kcuzner/kl2-dev/firmware/include/MKL26Z4.h

/*
** ###################################################################
**     Processors:          MKL26Z128VFM4
**                          MKL26Z64VFM4
**                          MKL26Z32VM4
**                          MKL26Z128VFT4
**                          MKL26Z64VFT4
**                          MKL26Z32VFT4
**                          MKL26Z256VLH4
**                          MKL26Z128VLH4
**                          MKL26Z64VLH4
**                          MKL26Z32VLH4
**                          MKL26Z256VLK4
**                          MKL26Z256VLL4
**                          MKL26Z128VLL4
**                          MKL26Z256VMC4
**                          MKL26Z128VMC4
**
**     Compilers:           ARM Compiler
**                          Freescale C/C++ for Embedded ARM
**                          GNU C Compiler
**                          IAR ANSI C/C++ Compiler for ARM
**
**     Reference manual:    KL46P121M48SF4RM, Rev.1 Draft A, Aug 2012
**     Version:             rev. 1.0, 2012-12-12
**
**     Abstract:
**         This header file implements peripheral memory map for MKL26Z4
**         processor.
**
**     Copyright: 1997 - 2012 Freescale, Inc. All Rights Reserved.
**
**     http:                 www.freescale.com
**     mail:                 support@freescale.com
**
**     Revisions:
**     - rev. 1.0 (2012-12-12)
**         Initial version.
**
** ###################################################################
*/

/**
 * @file MKL26Z4.h
 * @version 1.0
 * @date 2012-12-12
 * @brief Peripheral memory map for MKL26Z4
 *
 * This header file implements peripheral memory map for MKL26Z4 processor.
 */


/* ----------------------------------------------------------------------------
   -- MCU activation
   ---------------------------------------------------------------------------- */

/* Prevention from multiple including the same memory map */
#if !defined(MCU_MKL26Z4)  /* Check if memory map has not been already included */
#define MCU_MKL26Z4

/* Check if another memory map has not been also included */
#if (defined(MCU_ACTIVE))
  #error MKL26Z4 memory map: There is already included another memory map. Only one memory map can be included.
#endif /* (defined(MCU_ACTIVE)) */
#define MCU_ACTIVE

#include <stdint.h>

/** Memory map major version (memory maps with equal major version number are
 * compatible) */
#define MCU_MEM_MAP_VERSION 0x0100u
/** Memory map minor version */
#define MCU_MEM_MAP_VERSION_MINOR 0x0000u


/* ----------------------------------------------------------------------------
   -- Interrupt vector numbers
   ---------------------------------------------------------------------------- */

/**
 * @addtogroup Interrupt_vector_numbers Interrupt vector numbers
 * @{
 */

/** Interrupt Number Definitions */
typedef enum {
  INT_Initial_Stack_Pointer    = 0,                /**< Initial stack pointer */
  INT_Initial_Program_Counter  = 1,                /**< Initial program counter */
  INT_NMI                      = 2,                /**< Non-maskable interrupt */
  INT_Hard_Fault               = 3,                /**< Hard fault exception */
  INT_Reserved4                = 4,                /**< Reserved interrupt 4 */
  INT_Reserved5                = 5,                /**< Reserved interrupt 5 */
  INT_Reserved6                = 6,                /**< Reserved interrupt 6 */
  INT_Reserved7                = 7,                /**< Reserved interrupt 7 */
  INT_Reserved8                = 8,                /**< Reserved interrupt 8 */
  INT_Reserved9                = 9,                /**< Reserved interrupt 9 */
  INT_Reserved10               = 10,               /**< Reserved interrupt 10 */
  INT_SVCall                   = 11,               /**< A supervisor call exception */
  INT_Reserved12               = 12,               /**< Reserved interrupt 12 */
  INT_Reserved13               = 13,               /**< Reserved interrupt 13 */
  INT_PendableSrvReq           = 14,               /**< PendSV exception - request for system level service */
  INT_SysTick                  = 15,               /**< SysTick interrupt */
  INT_DMA0                     = 16,               /**< DMA channel 0 transfer complete/error interrupt */
  INT_DMA1                     = 17,               /**< DMA channel 1 transfer complete/error interrupt */
  INT_DMA2                     = 18,               /**< DMA channel 2 transfer complete/error interrupt */
  INT_DMA3                     = 19,               /**< DMA channel 3 transfer complete/error interrupt */
  INT_Reserved20               = 20,               /**< Reserved interrupt 20 */
  INT_FTFA                     = 21,               /**< FTFA command complete/read collision interrupt */
  INT_LVD_LVW                  = 22,               /**< Low Voltage Detect, Low Voltage Warning */
  INT_LLW                      = 23,               /**< Low Leakage Wakeup */
  INT_I2C0                     = 24,               /**< I2C0 interrupt */
  INT_I2C1                     = 25,               /**< I2C0 interrupt 25 */
  INT_SPI0                     = 26,               /**< SPI0 interrupt */
  INT_SPI1                     = 27,               /**< SPI1 interrupt */
  INT_UART0                    = 28,               /**< UART0 status/error interrupt */
  INT_UART1                    = 29,               /**< UART1 status/error interrupt */
  INT_UART2                    = 30,               /**< UART2 status/error interrupt */
  INT_ADC0                     = 31,               /**< ADC0 interrupt */
  INT_CMP0                     = 32,               /**< CMP0 interrupt */
  INT_TPM0                     = 33,               /**< TPM0 fault, overflow and channels interrupt */
  INT_TPM1                     = 34,               /**< TPM1 fault, overflow and channels interrupt */
  INT_TPM2                     = 35,               /**< TPM2 fault, overflow and channels interrupt */
  INT_RTC                      = 36,               /**< RTC interrupt */
  INT_RTC_Seconds              = 37,               /**< RTC seconds interrupt */
  INT_PIT                      = 38,               /**< PIT timer interrupt */
  INT_I2S0                     = 39,               /**< I2S0 transmit interrupt */
  INT_USB0                     = 40,               /**< USB0 interrupt */
  INT_DAC0                     = 41,               /**< DAC0 interrupt */
  INT_TSI0                     = 42,               /**< TSI0 interrupt */
  INT_MCG                      = 43,               /**< MCG interrupt */
  INT_LPTimer                  = 44,               /**< LPTimer interrupt */
  INT_Reserved45               = 45,               /**< Reserved interrupt 45 */
  INT_PORTA                    = 46,               /**< Port A interrupt */
  INT_PORTD                    = 47                /**< Port D interrupt */
} IRQInterruptIndex;

/**
 * @}
 */ /* end of group Interrupt_vector_numbers */


/* ----------------------------------------------------------------------------
   -- Peripheral type defines
   ---------------------------------------------------------------------------- */

/**
 * @addtogroup Peripheral_defines Peripheral type defines
 * @{
 */


/*
** Start of section using anonymous unions
*/

#if defined(__ARMCC_VERSION)
  #pragma push
  #pragma anon_unions
#elif defined(__CWCC__)
  #pragma push
  #pragma cpp_extensions on
#elif defined(__GNUC__)
  /* anonymous unions are enabled by default */
#elif defined(__IAR_SYSTEMS_ICC__)
  #pragma language=extended
#else
  #error Not supported compiler type
#endif

/* ----------------------------------------------------------------------------
   -- ADC
   ---------------------------------------------------------------------------- */

/**
 * @addtogroup ADC_Peripheral ADC
 * @{
 */

/** ADC - Peripheral register structure */
typedef struct ADC_MemMap {
  uint32_t SC1[2];                                 /**< ADC Status and Control Registers 1, array offset: 0x0, array step: 0x4 */
  uint32_t CFG1;                                   /**< ADC Configuration Register 1, offset: 0x8 */
  uint32_t CFG2;                                   /**< ADC Configuration Register 2, offset: 0xC */
  uint32_t R[2];                                   /**< ADC Data Result Register, array offset: 0x10, array step: 0x4 */
  uint32_t CV1;                                    /**< Compare Value Registers, offset: 0x18 */
  uint32_t CV2;                                    /**< Compare Value Registers, offset: 0x1C */
  uint32_t SC2;                                    /**< Status and Control Register 2, offset: 0x20 */
  uint32_t SC3;                                    /**< Status and Control Register 3, offset: 0x24 */
  uint32_t OFS;                                    /**< ADC Offset Correction Register, offset: 0x28 */
  uint32_t PG;                                     /**< ADC Plus-Side Gain Register, offset: 0x2C */
  uint32_t MG;                                     /**< ADC Minus-Side Gain Register, offset: 0x30 */
  uint32_t CLPD;                                   /**< ADC Plus-Side General Calibration Value Register, offset: 0x34 */
  uint32_t CLPS;                                   /**< ADC Plus-Side General Calibration Value Register, offset: 0x38 */
  uint32_t CLP4;                                   /**< ADC Plus-Side General Calibration Value Register, offset: 0x3C */
  uint32_t CLP3;                                   /**< ADC Plus-Side General Calibration Value Register, offset: 0x40 */
  uint32_t CLP2;                                   /**< ADC Plus-Side General Calibration Value Register, offset: 0x44 */
  uint32_t CLP1;                                   /**< ADC Plus-Side General Calibration Value Register, offset: 0x48 */
  uint32_t CLP0;                                   /**< ADC Plus-Side General Calibration Value Register, offset: 0x4C */
  uint8_t RESERVED_0[4];
  uint32_t CLMD;                                   /**< ADC Minus-Side General Calibration Value Register, offset: 0x54 */
  uint32_t CLMS;                                   /**< ADC Minus-Side General Calibration Value Register, offset: 0x58 */
  uint32_t CLM4;                                   /**< ADC Minus-Side General Calibration Value Register, offset: 0x5C */
  uint32_t CLM3;                                   /**< ADC Minus-Side General Calibration Value Register, offset: 0x60 */
  uint32_t CLM2;                                   /**< ADC Minus-Side General Calibration Value Register, offset: 0x64 */
  uint32_t CLM1;                                   /**< ADC Minus-Side General Calibration Value Register, offset: 0x68 */
  uint32_t CLM0;                                   /**< ADC Minus-Side General Calibration Value Register, offset: 0x6C */
} volatile *ADC_MemMapPtr;

/* ----------------------------------------------------------------------------
   -- ADC - Register accessor macros
   ---------------------------------------------------------------------------- */

/**
 * @addtogroup ADC_Register_Accessor_Macros ADC - Register accessor macros
 * @{
 */


/* ADC - Register accessors */
#define ADC_SC1_REG(base,index)                  ((base)->SC1[index])
#define ADC_CFG1_REG(base)                       ((base)->CFG1)
#define ADC_CFG2_REG(base)                       ((base)->CFG2)
#define ADC_R_REG(base,index)                    ((base)->R[index])
#define ADC_CV1_REG(base)                        ((base)->CV1)
#define ADC_CV2_REG(base)                        ((base)->CV2)
#define ADC_SC2_REG(base)                        ((base)->SC2)
#define ADC_SC3_REG(base)                        ((base)->SC3)
#define ADC_OFS_REG(base)                        ((base)->OFS)
#define ADC_PG_REG(base)                         ((base)->PG)
#define ADC_MG_REG(base)                         ((base)->MG)
#define ADC_CLPD_REG(base)                       ((base)->CLPD)
#define ADC_CLPS_REG(base)                       ((base)->CLPS)
#define ADC_CLP4_REG(base)                       ((base)->CLP4)
#define ADC_CLP3_REG(base)                       ((base)->CLP3)
#define ADC_CLP2_REG(base)                       ((base)->CLP2)
#define ADC_CLP1_REG(base)                       ((base)->CLP1)
#define ADC_CLP0_REG(base)                       ((base)->CLP0)
#define ADC_CLMD_REG(base)                       ((base)->CLMD)
#define ADC_CLMS_REG(base)                       ((base)->CLMS)
#define ADC_CLM4_REG(base)                       ((base)->CLM4)
#define ADC_CLM3_REG(base)                       ((base)->CLM3)
#define ADC_CLM2_REG(base)                       ((base)->CLM2)
#define ADC_CLM1_REG(base)                       ((base)->CLM1)
#define ADC_CLM0_REG(base)                       ((base)->CLM0)

/**
 * @}
 */ /* end of group ADC_Register_Accessor_Macros */


/* ----------------------------------------------------------------------------
   -- ADC Register Masks
   ---------------------------------------------------------------------------- */

/**
 * @addtogroup ADC_Register_Masks ADC Register Masks
 * @{
 */

/* SC1 Bit Fields */
#define ADC_SC1_ADCH_MASK                        0x1Fu
#define ADC_SC1_ADCH_SHIFT                       0
#define ADC_SC1_ADCH(x)                          (((uint32_t)(((uint32_t)(x))<<ADC_SC1_ADCH_SHIFT))&ADC_SC1_ADCH_MASK)
#define ADC_SC1_DIFF_MASK                        0x20u
#define ADC_SC1_DIFF_SHIFT                       5
#define ADC_SC1_AIEN_MASK                        0x40u
#define ADC_SC1_AIEN_SHIFT                       6
#define ADC_SC1_COCO_MASK                        0x80u
#define ADC_SC1_COCO_SHIFT                       7
/* CFG1 Bit Fields */
#define ADC_CFG1_ADICLK_MASK                     0x3u
#define ADC_CFG1_ADICLK_SHIFT                    0
#define ADC_CFG1_ADICLK(x)                       (((uint32_t)(((uint32_t)(x))<<ADC_CFG1_ADICLK_SHIFT))&ADC_CFG1_ADICLK_MASK)
#define ADC_CFG1_MODE_MASK                       0xCu
#define ADC_CFG1_MODE_SHIFT                      2
#define ADC_CFG1_MODE(x)                         (((uint32_t)(((uint32_t)(x))<<ADC_CFG1_MODE_SHIFT))&ADC_CFG1_MODE_MASK)
#define ADC_CFG1_ADLSMP_MASK                     0x10u
#define ADC_CFG1_ADLSMP_SHIFT                    4
#define ADC_CFG1_ADIV_MASK                       0x60u
#define ADC_CFG1_ADIV_SHIFT                      5
#define ADC_CFG1_ADIV(x)                         (((uint32_t)(((uint32_t)(x))<<ADC_CFG1_ADIV_SHIFT))&ADC_CFG1_ADIV_MASK)
#define ADC_CFG1_ADLPC_MASK                      0x80u
#define ADC_CFG1_ADLPC_SHIFT                     7
/* CFG2 Bit Fields */
#define ADC_CFG2_ADLSTS_MASK                     0x3u
#define ADC_CFG2_ADLSTS_SHIFT                    0
#define ADC_CFG2_ADLSTS(x)                       (((uint32_t)(((uint32_t)(x))<<ADC_CFG2_ADLSTS_SHIFT))&ADC_CFG2_ADLSTS_MASK)
#define ADC_CFG2_ADHSC_MASK                      0x4u
#define ADC_CFG2_ADHSC_SHIFT                     2
#define ADC_CFG2_ADACKEN_MASK                    0x8u
#define ADC_CFG2_ADACKEN_SHIFT                   3
#define ADC_CFG2_MUXSEL_MASK                     0x10u
#define ADC_CFG2_MUXSEL_SHIFT                    4
/* R Bit Fields */
#define ADC_R_D_MASK                             0xFFFFu
#define ADC_R_D_SHIFT                            0
#define ADC_R_D(x)                               (((uint32_t)(((uint32_t)(x))<<ADC_R_D_SHIFT))&ADC_R_D_MASK)
/* CV1 Bit Fields */
#define ADC_CV1_CV_MASK                          0xFFFFu
#define ADC_CV1_CV_SHIFT                         0
#define ADC_CV1_CV(x)                            (((uint32_t)(((uint32_t)(x))<<ADC_CV1_CV_SHIFT))&ADC_CV1_CV_MASK)
/* CV2 Bit Fields */
#define ADC_CV2_CV_MASK                          0xFFFFu
#define ADC_CV2_CV_SHIFT                         0
#define ADC_CV2_CV(x)                            (((uint32_t)(((uint32_t)(x))<<ADC_CV2_CV_SHIFT))&ADC_CV2_CV_MASK)
/* SC2 Bit Fields */
#define ADC_SC2_REFSEL_MASK                      0x3u
#define ADC_SC2_REFSEL_SHIFT                     0
#define ADC_SC2_REFSEL(x)                        (((uint32_t)(((uint32_t)(x))<<ADC_SC2_REFSEL_SHIFT))&ADC_SC2_REFSEL_MASK)
#define ADC_SC2_DMAEN_MASK                       0x4u
#define ADC_SC2_DMAEN_SHIFT                      2
#define ADC_SC2_ACREN_MASK                       0x8u
#define ADC_SC2_ACREN_SHIFT                      3
#define ADC_SC2_ACFGT_MASK                       0x10u
#define ADC_SC2_ACFGT_SHIFT                      4
#define ADC_SC2_ACFE_MASK                        0x20u
#define ADC_SC2_ACFE_SHIFT                       5
#define ADC_SC2_ADTRG_MASK                       0x40u
#define ADC_SC2_ADTRG_SHIFT                      6
#define ADC_SC2_ADACT_MASK                       0x80u
#define ADC_SC2_ADACT_SHIFT                      7
/* SC3 Bit Fields */
#define ADC_SC3_AVGS_MASK                        0x3u
#define ADC_SC3_AVGS_SHIFT                       0
#define ADC_SC3_AVGS(x)                          (((uint32_t)(((uint32_t)(x))<<ADC_SC3_AVGS_SHIFT))&ADC_SC3_AVGS_MASK)
#define ADC_SC3_AVGE_MASK                        0x4u
#define ADC_SC3_AVGE_SHIFT                       2
#define ADC_SC3_ADCO_MASK                        0x8u
#define ADC_SC3_ADCO_SHIFT                       3
#define ADC_SC3_CALF_MASK                        0x40u
#define ADC_SC3_CALF_SHIFT                       6
#define ADC_SC3_CAL_MASK                         0x80u
#define ADC_SC3_CAL_SHIFT                        7
/* OFS Bit Fields */
#define ADC_OFS_OFS_MASK                         0xFFFFu
#define ADC_OFS_OFS_SHIFT                        0
#define ADC_OFS_OFS(x)                           (((uint32_t)(((uint32_t)(x))<<ADC_OFS_OFS_SHIFT))&ADC_OFS_OFS_MASK)
/* PG Bit Fields */
#define ADC_PG_PG_MASK                           0xFFFFu
#define ADC_PG_PG_SHIFT                          0
#define ADC_PG_PG(x)                             (((uint32_t)(((uint32_t)(x))<<ADC_PG_PG_SHIFT))&ADC_PG_PG_MASK)
/* MG Bit Fields */
#define ADC_MG_MG_MASK                           0xFFFFu
#define ADC_MG_MG_SHIFT                          0
#define ADC_MG_MG(x)                             (((uint32_t)(((uint32_t)(x))<<ADC_MG_MG_SHIFT))&ADC_MG_MG_MASK)
/* CLPD Bit Fields */
#define ADC_CLPD_CLPD_MASK                       0x3Fu
#define ADC_CLPD_CLPD_SHIFT                      0
#define ADC_CLPD_CLPD(x)                         (((uint32_t)(((uint32_t)(x))<<ADC_CLPD_CLPD_SHIFT))&ADC_CLPD_CLPD_MASK)
/* CLPS Bit Fields */
#define ADC_CLPS_CLPS_MASK                       0x3Fu
#define ADC_CLPS_CLPS_SHIFT                      0
#define ADC_CLPS_CLPS(x)                         (((uint32_t)(((uint32_t)(x))<<ADC_CLPS_CLPS_SHIFT))&ADC_CLPS_CLPS_MASK)
/* CLP4 Bit Fields */
#define ADC_CLP4_CLP4_MASK                       0x3FFu
#define ADC_CLP4_CLP4_SHIFT                      0
#define ADC_CLP4_CLP4(x)                         (((uint32_t)(((uint32_t)(x))<<ADC_CLP4_CLP4_SHIFT))&ADC_CLP4_CLP4_MASK)
/* CLP3 Bit Fields */
#define ADC_CLP3_CLP3_MASK                       0x1FFu
#define ADC_CLP3_CLP3_SHIFT                      0
#define ADC_CLP3_CLP3(x)                         (((uint32_t)(((uint32_t)(x))<<ADC_CLP3_CLP3_SHIFT))&ADC_CLP3_CLP3_MASK)
/* CLP2 Bit Fields */
#define ADC_CLP2_CLP2_MASK                       0xFFu
#define ADC_CLP2_CLP2_SHIFT                      0
#define ADC_CLP2_CLP2(x)                         (((uint32_t)(((uint32_t)(x))<<ADC_CLP2_CLP2_SHIFT))&ADC_CLP2_CLP2_MASK)
/* CLP1 Bit Fields */
#define ADC_CLP1_CLP1_MASK                       0x7Fu
#define ADC_CLP1_CLP1_SHIFT                      0
#define ADC_CLP1_CLP1(x)                         (((uint32_t)(((uint32_t)(x))<<ADC_CLP1_CLP1_SHIFT))&ADC_CLP1_CLP1_MASK)
/* CLP0 Bit Fields */
#define ADC_CLP0_CLP0_MASK                       0x3Fu
#define ADC_CLP0_CLP0_SHIFT                      0
#define ADC_CLP0_CLP0(x)                         (((uint32_t)(((uint32_t)(x))<<ADC_CLP0_CLP0_SHIFT))&ADC_CLP0_CLP0_MASK)
/* CLMD Bit Fields */
#define ADC_CLMD_CLMD_MASK                       0x3Fu
#define ADC_CLMD_CLMD_SHIFT                      0
#define ADC_CLMD_CLMD(x)                         (((uint32_t)(((uint32_t)(x))<<ADC_CLMD_CLMD_SHIFT))&ADC_CLMD_CLMD_MASK)
/* CLMS Bit Fields */
#define ADC_CLMS_CLMS_MASK                       0x3Fu
#define ADC_CLMS_CLMS_SHIFT                      0
#define ADC_CLMS_CLMS(x)                         (((uint32_t)(((uint32_t)(x))<<ADC_CLMS_CLMS_SHIFT))&ADC_CLMS_CLMS_MASK)
/* CLM4 Bit Fields */
#define ADC_CLM4_CLM4_MASK                       0x3FFu
#define ADC_CLM4_CLM4_SHIFT                      0
#define ADC_CLM4_CLM4(x)                         (((uint32_t)(((uint32_t)(x))<<ADC_CLM4_CLM4_SHIFT))&ADC_CLM4_CLM4_MASK)
/* CLM3 Bit Fields */
#define ADC_CLM3_CLM3_MASK                       0x1FFu
#define ADC_CLM3_CLM3_SHIFT                      0
#define ADC_CLM3_CLM3(x)                         (((uint32_t)(((uint32_t)(x))<<ADC_CLM3_CLM3_SHIFT))&ADC_CLM3_CLM3_MASK)
/* CLM2 Bit Fields */
#define ADC_CLM2_CLM2_MASK                       0xFFu
#define ADC_CLM2_CLM2_SHIFT                      0
#define ADC_CLM2_CLM2(x)                         (((uint32_t)(((uint32_t)(x))<<ADC_CLM2_CLM2_SHIFT))&ADC_CLM2_CLM2_MASK)
/* CLM1 Bit Fields */
#define ADC_CLM1_CLM1_MASK                       0x7Fu
#define ADC_CLM1_CLM1_SHIFT                      0
#define ADC_CLM1_CLM1(x)                         (((uint32_t)(((uint32_t)(x))<<ADC_CLM1_CLM1_SHIFT))&ADC_CLM1_CLM1_MASK)
/* CLM0 Bit Fields */
#define ADC_CLM0_CLM0_MASK                       0x3Fu
#define ADC_CLM0_CLM0_SHIFT                      0
#define ADC_CLM0_CLM0(x)                         (((uint32_t)(((uint32_t)(x))<<ADC_CLM0_CLM0_SHIFT))&ADC_CLM0_CLM0_MASK)

/**
 * @}
 */ /* end of group ADC_Register_Masks */


/* ADC - Peripheral instance base addresses */
/** Peripheral ADC0 base pointer */
#define ADC0_BASE_PTR                            ((ADC_MemMapPtr)0x4003B000u)
/** Array initializer of ADC peripheral base pointers */
#define ADC_BASE_PTRS                            { ADC0_BASE_PTR }

/* ----------------------------------------------------------------------------
   -- ADC - Register accessor macros
   ---------------------------------------------------------------------------- */

/**
 * @addtogroup ADC_Register_Accessor_Macros ADC - Register accessor macros
 * @{
 */


/* ADC - Register instance definitions */
/* ADC0 */
#define ADC0_SC1A                                ADC_SC1_REG(ADC0_BASE_PTR,0)
#define ADC0_SC1B                                ADC_SC1_REG(ADC0_BASE_PTR,1)
#define ADC0_CFG1                                ADC_CFG1_REG(ADC0_BASE_PTR)
#define ADC0_CFG2                                ADC_CFG2_REG(ADC0_BASE_PTR)
#define ADC0_RA                                  ADC_R_REG(ADC0_BASE_PTR,0)
#define ADC0_RB                                  ADC_R_REG(ADC0_BASE_PTR,1)
#define ADC0_CV1                                 ADC_CV1_REG(ADC0_BASE_PTR)
#define ADC0_CV2                                 ADC_CV2_REG(ADC0_BASE_PTR)
#define ADC0_SC2                                 ADC_SC2_REG(ADC0_BASE_PTR)
#define ADC0_SC3                                 ADC_SC3_REG(ADC0_BASE_PTR)
#define ADC0_OFS                                 ADC_OFS_REG(ADC0_BASE_PTR)
#define ADC0_PG                                  ADC_PG_REG(ADC0_BASE_PTR)
#define ADC0_MG                                  ADC_MG_REG(ADC0_BASE_PTR)
#define ADC0_CLPD                                ADC_CLPD_REG(ADC0_BASE_PTR)
#define ADC0_CLPS                                ADC_CLPS_REG(ADC0_BASE_PTR)
#define ADC0_CLP4                                ADC_CLP4_REG(ADC0_BASE_PTR)
#define ADC0_CLP3                                ADC_CLP3_REG(ADC0_BASE_PTR)
#define ADC0_CLP2                                ADC_CLP2_REG(ADC0_BASE_PTR)
#define ADC0_CLP1                                ADC_CLP1_REG(ADC0_BASE_PTR)
#define ADC0_CLP0                                ADC_CLP0_REG(ADC0_BASE_PTR)
#define ADC0_CLMD                                ADC_CLMD_REG(ADC0_BASE_PTR)
#define ADC0_CLMS                                ADC_CLMS_REG(ADC0_BASE_PTR)
#define ADC0_CLM4                                ADC_CLM4_REG(ADC0_BASE_PTR)
#define ADC0_CLM3                                ADC_CLM3_REG(ADC0_BASE_PTR)
#define ADC0_CLM2                                ADC_CLM2_REG(ADC0_BASE_PTR)
#define ADC0_CLM1                                ADC_CLM1_REG(ADC0_BASE_PTR)
#define ADC0_CLM0                                ADC_CLM0_REG(ADC0_BASE_PTR)

/* ADC - Register array accessors */
#define ADC0_SC1(index)                          ADC_SC1_REG(ADC0_BASE_PTR,index)
#define ADC0_R(index)                            ADC_R_REG(ADC0_BASE_PTR,index)

/**
 * @}
 */ /* end of group ADC_Register_Accessor_Macros */


/**
 * @}
 */ /* end of group ADC_Peripheral */


/* ----------------------------------------------------------------------------
   -- BP
   ---------------------------------------------------------------------------- */

/**
 * @addtogroup BP_Peripheral BP
 * @{
 */

/** BP - Peripheral register structure */
typedef struct BP_MemMap {
  uint32_t CTRL;                                   /**< FlashPatch Control Register, offset: 0x0 */
  uint8_t RESERVED_0[4];
  uint32_t COMP[2];                                /**< FlashPatch Comparator Register 0..FlashPatch Comparator Register 1, array offset: 0x8, array step: 0x4 */
  uint8_t RESERVED_1[4032];
  uint32_t PID4;                                   /**< Peripheral Identification Register 4., offset: 0xFD0 */
  uint32_t PID5;                                   /**< Peripheral Identification Register 5., offset: 0xFD4 */
  uint32_t PID6;                                   /**< Peripheral Identification Register 6., offset: 0xFD8 */
  uint32_t PID7;                                   /**< Peripheral Identification Register 7., offset: 0xFDC */
  uint32_t PID0;                                   /**< Peripheral Identification Register 0., offset: 0xFE0 */
  uint32_t PID1;                                   /**< Peripheral Identification Register 1., offset: 0xFE4 */
  uint32_t PID2;                                   /**< Peripheral Identification Register 2., offset: 0xFE8 */
  uint32_t PID3;                                   /**< Peripheral Identification Register 3., offset: 0xFEC */
  uint32_t CID0;                                   /**< Component Identification Register 0., offset: 0xFF0 */
  uint32_t CID1;                                   /**< Component Identification Register 1., offset: 0xFF4 */
  uint32_t CID2;                                   /**< Component Identification Register 2., offset: 0xFF8 */
  uint32_t CID3;                                   /**< Component Identification Register 3., offset: 0xFFC */
} volatile *BP_MemMapPtr;

/* ----------------------------------------------------------------------------
   -- BP - Register accessor macros
   ---------------------------------------------------------------------------- */

/**
 * @addtogroup BP_Register_Accessor_Macros BP - Register accessor macros
 * @{
 */


/* BP - Register accessors */
#define BP_CTRL_REG(base)                        ((base)->CTRL)
#define BP_COMP_REG(base,index)                  ((base)->COMP[index])
#define BP_PID4_REG(base)                        ((base)->PID4)
#define BP_PID5_REG(base)                        ((base)->PID5)
#define BP_PID6_REG(base)                        ((base)->PID6)
#define BP_PID7_REG(base)                        ((base)->PID7)
#define BP_PID0_REG(base)                        ((base)->PID0)
#define BP_PID1_REG(base)                        ((base)->PID1)
#define BP_PID2_REG(base)                        ((base)->PID2)
#define BP_PID3_REG(base)                        ((base)->PID3)
#define BP_CID0_REG(base)                        ((base)->CID0)
#define BP_CID1_REG(base)                        ((base)->CID1)
#define BP_CID2_REG(base)                        ((base)->CID2)
#define BP_CID3_REG(base)                        ((base)->CID3)

/**
 * @}
 */ /* end of group BP_Register_Accessor_Macros */


/* ----------------------------------------------------------------------------
   -- BP Register Masks
   ---------------------------------------------------------------------------- */

/**
 * @addtogroup BP_Register_Masks BP Register Masks
 * @{
 */


/**
 * @}
 */ /* end of group BP_Register_Masks */


/* BP - Peripheral instance base addresses */
/** Peripheral BP base pointer */
#define BP_BASE_PTR                              ((BP_MemMapPtr)0xE0002000u)
/** Array initializer of BP peripheral base pointers */
#define BP_BASE_PTRS                             { BP_BASE_PTR }

/* ----------------------------------------------------------------------------
   -- BP - Register accessor macros
   ---------------------------------------------------------------------------- */

/**
 * @addtogroup BP_Register_Accessor_Macros BP - Register accessor macros
 * @{
 */


/* BP - Register instance definitions */
/* BP */
#define BP_CTRL                                  BP_CTRL_REG(BP_BASE_PTR)
#define BP_COMP0                                 BP_COMP_REG(BP_BASE_PTR,0)
#define BP_COMP1                                 BP_COMP_REG(BP_BASE_PTR,1)
#define BP_PID4                                  BP_PID4_REG(BP_BASE_PTR)
#define BP_PID5                                  BP_PID5_REG(BP_BASE_PTR)
#define BP_PID6                                  BP_PID6_REG(BP_BASE_PTR)
#define BP_PID7                                  BP_PID7_REG(BP_BASE_PTR)
#define BP_PID0                                  BP_PID0_REG(BP_BASE_PTR)
#define BP_PID1                                  BP_PID1_REG(BP_BASE_PTR)
#define BP_PID2                                  BP_PID2_REG(BP_BASE_PTR)
#define BP_PID3                                  BP_PID3_REG(BP_BASE_PTR)
#define BP_CID0                                  BP_CID0_REG(BP_BASE_PTR)
#define BP_CID1                                  BP_CID1_REG(BP_BASE_PTR)
#define BP_CID2                                  BP_CID2_REG(BP_BASE_PTR)
#define BP_CID3                                  BP_CID3_REG(BP_BASE_PTR)

/* BP - Register array accessors */
#define BP_COMP(index)                           BP_COMP_REG(BP_BASE_PTR,index)

/**
 * @}
 */ /* end of group BP_Register_Accessor_Macros */


/**
 * @}
 */ /* end of group BP_Peripheral */


/* ----------------------------------------------------------------------------
   -- CMP
   ---------------------------------------------------------------------------- */

/**
 * @addtogroup CMP_Peripheral CMP
 * @{
 */

/** CMP - Peripheral register structure */
typedef struct CMP_MemMap {
  uint8_t CR0;                                     /**< CMP Control Register 0, offset: 0x0 */
  uint8_t CR1;                                     /**< CMP Control Register 1, offset: 0x1 */
  uint8_t FPR;                                     /**< CMP Filter Period Register, offset: 0x2 */
  uint8_t SCR;                                     /**< CMP Status and Control Register, offset: 0x3 */
  uint8_t DACCR;                                   /**< DAC Control Register, offset: 0x4 */
  uint8_t MUXCR;                                   /**< MUX Control Register, offset: 0x5 */
} volatile *CMP_MemMapPtr;

/* ----------------------------------------------------------------------------
   -- CMP - Register accessor macros
   ---------------------------------------------------------------------------- */

/**
 * @addtogroup CMP_Register_Accessor_Macros CMP - Register accessor macros
 * @{
 */


/* CMP - Register accessors */
#define CMP_CR0_REG(base)                        ((base)->CR0)
#define CMP_CR1_REG(base)                        ((base)->CR1)
#define CMP_FPR_REG(base)                        ((base)->FPR)
#define CMP_SCR_REG(base)                        ((base)->SCR)
#define CMP_DACCR_REG(base)                      ((base)->DACCR)
#define CMP_MUXCR_REG(base)                      ((base)->MUXCR)

/**
 * @}
 */ /* end of group CMP_Register_Accessor_Macros */


/* ----------------------------------------------------------------------------
   -- CMP Register Masks
   ---------------------------------------------------------------------------- */

/**
 * @addtogroup CMP_Register_Masks CMP Register Masks
 * @{
 */

/* CR0 Bit Fields */
#define CMP_CR0_HYSTCTR_MASK                     0x3u
#define CMP_CR0_HYSTCTR_SHIFT                    0
#define CMP_CR0_HYSTCTR(x)                       (((uint8_t)(((uint8_t)(x))<<CMP_CR0_HYSTCTR_SHIFT))&CMP_CR0_HYSTCTR_MASK)
#define CMP_CR0_FILTER_CNT_MASK                  0x70u
#define CMP_CR0_FILTER_CNT_SHIFT                 4
#define CMP_CR0_FILTER_CNT(x)                    (((uint8_t)(((uint8_t)(x))<<CMP_CR0_FILTER_CNT_SHIFT))&CMP_CR0_FILTER_CNT_MASK)
/* CR1 Bit Fields */
#define CMP_CR1_EN_MASK                          0x1u
#define CMP_CR1_EN_SHIFT                         0
#define CMP_CR1_OPE_MASK                         0x2u
#define CMP_CR1_OPE_SHIFT                        1
#define CMP_CR1_COS_MASK                         0x4u
#define CMP_CR1_COS_SHIFT                        2
#define CMP_CR1_INV_MASK                         0x8u
#define CMP_CR1_INV_SHIFT                        3
#define CMP_CR1_PMODE_MASK                       0x10u
#define CMP_CR1_PMODE_SHIFT                      4
#define CMP_CR1_TRIGM_MASK                       0x20u
#define CMP_CR1_TRIGM_SHIFT                      5
#define CMP_CR1_WE_MASK                          0x40u
#define CMP_CR1_WE_SHIFT                         6
#define CMP_CR1_SE_MASK                          0x80u
#define CMP_CR1_SE_SHIFT                         7
/* FPR Bit Fields */
#define CMP_FPR_FILT_PER_MASK                    0xFFu
#define CMP_FPR_FILT_PER_SHIFT                   0
#define CMP_FPR_FILT_PER(x)                      (((uint8_t)(((uint8_t)(x))<<CMP_FPR_FILT_PER_SHIFT))&CMP_FPR_FILT_PER_MASK)
/* SCR Bit Fields */
#define CMP_SCR_COUT_MASK                        0x1u
#define CMP_SCR_COUT_SHIFT                       0
#define CMP_SCR_CFF_MASK                         0x2u
#define CMP_SCR_CFF_SHIFT                        1
#define CMP_SCR_CFR_MASK                         0x4u
#define CMP_SCR_CFR_SHIFT                        2
#define CMP_SCR_IEF_MASK                         0x8u
#define CMP_SCR_IEF_SHIFT                        3
#define CMP_SCR_IER_MASK                         0x10u
#define CMP_SCR_IER_SHIFT                        4
#define CMP_SCR_DMAEN_MASK                       0x40u
#define CMP_SCR_DMAEN_SHIFT                      6
/* DACCR Bit Fields */
#define CMP_DACCR_VOSEL_MASK                     0x3Fu
#define CMP_DACCR_VOSEL_SHIFT                    0
#define CMP_DACCR_VOSEL(x)                       (((uint8_t)(((uint8_t)(x))<<CMP_DACCR_VOSEL_SHIFT))&CMP_DACCR_VOSEL_MASK)
#define CMP_DACCR_VRSEL_MASK                     0x40u
#define CMP_DACCR_VRSEL_SHIFT                    6
#define CMP_DACCR_DACEN_MASK                     0x80u
#define CMP_DACCR_DACEN_SHIFT                    7
/* MUXCR Bit Fields */
#define CMP_MUXCR_MSEL_MASK                      0x7u
#define CMP_MUXCR_MSEL_SHIFT                     0
#define CMP_MUXCR_MSEL(x)                        (((uint8_t)(((uint8_t)(x))<<CMP_MUXCR_MSEL_SHIFT))&CMP_MUXCR_MSEL_MASK)
#define CMP_MUXCR_PSEL_MASK                      0x38u
#define CMP_MUXCR_PSEL_SHIFT                     3
#define CMP_MUXCR_PSEL(x)                        (((uint8_t)(((uint8_t)(x))<<CMP_MUXCR_PSEL_SHIFT))&CMP_MUXCR_PSEL_MASK)
#define CMP_MUXCR_PSTM_MASK                      0x80u
#define CMP_MUXCR_PSTM_SHIFT                     7

/**
 * @}
 */ /* end of group CMP_Register_Masks */


/* CMP - Peripheral instance base addresses */
/** Peripheral CMP0 base pointer */
#define CMP0_BASE_PTR                            ((CMP_MemMapPtr)0x40073000u)
/** Array initializer of CMP peripheral base pointers */
#define CMP_BASE_PTRS                            { CMP0_BASE_PTR }

/* ----------------------------------------------------------------------------
   -- CMP - Register accessor macros
   ---------------------------------------------------------------------------- */

/**
 * @addtogroup CMP_Register_Accessor_Macros CMP - Register accessor macros
 * @{
 */


/* CMP - Register instance definitions */
/* CMP0 */
#define CMP0_CR0                                 CMP_CR0_REG(CMP0_BASE_PTR)
#define CMP0_CR1                                 CMP_CR1_REG(CMP0_BASE_PTR)
#define CMP0_FPR                                 CMP_FPR_REG(CMP0_BASE_PTR)
#define CMP0_SCR                                 CMP_SCR_REG(CMP0_BASE_PTR)
#define CMP0_DACCR                               CMP_DACCR_REG(CMP0_BASE_PTR)
#define CMP0_MUXCR                               CMP_MUXCR_REG(CMP0_BASE_PTR)

/**
 * @}
 */ /* end of group CMP_Register_Accessor_Macros */


/**
 * @}
 */ /* end of group CMP_Peripheral */


/* ----------------------------------------------------------------------------
   -- CoreDebug
   ---------------------------------------------------------------------------- */

/**
 * @addtogroup CoreDebug_Peripheral CoreDebug
 * @{
 */

/** CoreDebug - Peripheral register structure */
typedef struct CoreDebug_MemMap {
  union {                                          /* offset: 0x0 */
    uint32_t base_DHCSR_Read;                        /**< Debug Halting Control and Status Register, offset: 0x0 */
    uint32_t base_DHCSR_Write;                       /**< Debug Halting Control and Status Register, offset: 0x0 */
  };
  uint32_t base_DCRSR;                             /**< Debug Core Register Selector Register, offset: 0x4 */
  uint32_t base_DCRDR;                             /**< Debug Core Register Data Register, offset: 0x8 */
  uint32_t base_DEMCR;                             /**< Debug Exception and Monitor Control Register, offset: 0xC */
} volatile *CoreDebug_MemMapPtr;

/* ----------------------------------------------------------------------------
   -- CoreDebug - Register accessor macros
   ---------------------------------------------------------------------------- */

/**
 * @addtogroup CoreDebug_Register_Accessor_Macros CoreDebug - Register accessor macros
 * @{
 */


/* CoreDebug - Register accessors */
#define CoreDebug_base_DHCSR_Read_REG(base)      ((base)->base_DHCSR_Read)
#define CoreDebug_base_DHCSR_Write_REG(base)     ((base)->base_DHCSR_Write)
#define CoreDebug_base_DCRSR_REG(base)           ((base)->base_DCRSR)
#define CoreDebug_base_DCRDR_REG(base)           ((base)->base_DCRDR)
#define CoreDebug_base_DEMCR_REG(base)           ((base)->base_DEMCR)

/**
 * @}
 */ /* end of group CoreDebug_Register_Accessor_Macros */


/* ----------------------------------------------------------------------------
   -- CoreDebug Register Masks
   ---------------------------------------------------------------------------- */

/**
 * @addtogroup CoreDebug_Register_Masks CoreDebug Register Masks
 * @{
 */


/**
 * @}
 */ /* end of group CoreDebug_Register_Masks */


/* CoreDebug - Peripheral instance base addresses */
/** Peripheral CoreDebug base pointer */
#define CoreDebug_BASE_PTR                       ((CoreDebug_MemMapPtr)0xE000EDF0u)
/** Array initializer of CoreDebug peripheral base pointers */
#define CoreDebug_BASE_PTRS                      { CoreDebug_BASE_PTR }

/* ----------------------------------------------------------------------------
   -- CoreDebug - Register accessor macros
   ---------------------------------------------------------------------------- */

/**
 * @addtogroup CoreDebug_Register_Accessor_Macros CoreDebug - Register accessor macros
 * @{
 */


/* CoreDebug - Register instance definitions */
/* CoreDebug */
#define DHCSR_Read                               CoreDebug_base_DHCSR_Read_REG(CoreDebug_BASE_PTR)
#define DHCSR_Write                              CoreDebug_base_DHCSR_Write_REG(CoreDebug_BASE_PTR)
#define DCRSR                                    CoreDebug_base_DCRSR_REG(CoreDebug_BASE_PTR)
#define DCRDR                                    CoreDebug_base_DCRDR_REG(CoreDebug_BASE_PTR)
#define DEMCR                                    CoreDebug_base_DEMCR_REG(CoreDebug_BASE_PTR)

/**
 * @}
 */ /* end of group CoreDebug_Register_Accessor_Macros */


/**
 * @}
 */ /* end of group CoreDebug_Peripheral */


/* ----------------------------------------------------------------------------
   -- DAC
   ---------------------------------------------------------------------------- */

/**
 * @addtogroup DAC_Peripheral DAC
 * @{
 */

/** DAC - Peripheral register structure */
typedef struct DAC_MemMap {
  struct {                                         /* offset: 0x0, array step: 0x2 */
    uint8_t DATL;                                    /**< DAC Data Low Register, array offset: 0x0, array step: 0x2 */
    uint8_t DATH;                                    /**< DAC Data High Register, array offset: 0x1, array step: 0x2 */
  } DAT[2];
  uint8_t RESERVED_0[28];
  uint8_t SR;                                      /**< DAC Status Register, offset: 0x20 */
  uint8_t C0;                                      /**< DAC Control Register, offset: 0x21 */
  uint8_t C1;                                      /**< DAC Control Register 1, offset: 0x22 */
  uint8_t C2;                                      /**< DAC Control Register 2, offset: 0x23 */
} volatile *DAC_MemMapPtr;

/* ----------------------------------------------------------------------------
   -- DAC - Register accessor macros
   ---------------------------------------------------------------------------- */

/**
 * @addtogroup DAC_Register_Accessor_Macros DAC - Register accessor macros
 * @{
 */


/* DAC - Register accessors */
#define DAC_DATL_REG(base,index)                 ((base)->DAT[index].DATL)
#define DAC_DATH_REG(base,index)                 ((base)->DAT[index].DATH)
#define DAC_SR_REG(base)                         ((base)->SR)
#define DAC_C0_REG(base)                         ((base)->C0)
#define DAC_C1_REG(base)                         ((base)->C1)
#define DAC_C2_REG(base)                         ((base)->C2)

/**
 * @}
 */ /* end of group DAC_Register_Accessor_Macros */


/* ----------------------------------------------------------------------------
   -- DAC Register Masks
   ---------------------------------------------------------------------------- */

/**
 * @addtogroup DAC_Register_Masks DAC Register Masks
 * @{
 */

/* DATL Bit Fields */
#define DAC_DATL_DATA0_MASK                      0xFFu
#define DAC_DATL_DATA0_SHIFT                     0
#define DAC_DATL_DATA0(x)                        (((uint8_t)(((uint8_t)(x))<<DAC_DATL_DATA0_SHIFT))&DAC_DATL_DATA0_MASK)
/* DATH Bit Fields */
#define DAC_DATH_DATA1_MASK                      0xFu
#define DAC_DATH_DATA1_SHIFT                     0
#define DAC_DATH_DATA1(x)                        (((uint8_t)(((uint8_t)(x))<<DAC_DATH_DATA1_SHIFT))&DAC_DATH_DATA1_MASK)
/* SR Bit Fields */
#define DAC_SR_DACBFRPBF_MASK                    0x1u
#define DAC_SR_DACBFRPBF_SHIFT                   0
#define DAC_SR_DACBFRPTF_MASK                    0x2u
#define DAC_SR_DACBFRPTF_SHIFT                   1
/* C0 Bit Fields */
#define DAC_C0_DACBBIEN_MASK                     0x1u
#define DAC_C0_DACBBIEN_SHIFT                    0
#define DAC_C0_DACBTIEN_MASK                     0x2u
#define DAC_C0_DACBTIEN_SHIFT                    1
#define DAC_C0_LPEN_MASK                         0x8u
#define DAC_C0_LPEN_SHIFT                        3
#define DAC_C0_DACSWTRG_MASK                     0x10u
#define DAC_C0_DACSWTRG_SHIFT                    4
#define DAC_C0_DACTRGSEL_MASK                    0x20u
#define DAC_C0_DACTRGSEL_SHIFT                   5
#define DAC_C0_DACRFS_MASK                       0x40u
#define DAC_C0_DACRFS_SHIFT                      6
#define DAC_C0_DACEN_MASK                        0x80u
#define DAC_C0_DACEN_SHIFT                       7
/* C1 Bit Fields */
#define DAC_C1_DACBFEN_MASK                      0x1u
#define DAC_C1_DACBFEN_SHIFT                     0
#define DAC_C1_DACBFMD_MASK                      0x4u
#define DAC_C1_DACBFMD_SHIFT                     2
#define DAC_C1_DMAEN_MASK                        0x80u
#define DAC_C1_DMAEN_SHIFT                       7
/* C2 Bit Fields */
#define DAC_C2_DACBFUP_MASK                      0x1u
#define DAC_C2_DACBFUP_SHIFT                     0
#define DAC_C2_DACBFRP_MASK                      0x10u
#define DAC_C2_DACBFRP_SHIFT                     4

/**
 * @}
 */ /* end of group DAC_Register_Masks */


/* DAC - Peripheral instance base addresses */
/** Peripheral DAC0 base pointer */
#define DAC0_BASE_PTR                            ((DAC_MemMapPtr)0x4003F000u)
/** Array initializer of DAC peripheral base pointers */
#define DAC_BASE_PTRS                            { DAC0_BASE_PTR }

/* ----------------------------------------------------------------------------
   -- DAC - Register accessor macros
   ---------------------------------------------------------------------------- */

/**
 * @addtogroup DAC_Register_Accessor_Macros DAC - Register accessor macros
 * @{
 */


/* DAC - Register instance definitions */
/* DAC0 */
#define DAC0_DAT0L                               DAC_DATL_REG(DAC0_BASE_PTR,0)
#define DAC0_DAT0H                               DAC_DATH_REG(DAC0_BASE_PTR,0)
#define DAC0_DAT1L                               DAC_DATL_REG(DAC0_BASE_PTR,1)
#define DAC0_DAT1H                               DAC_DATH_REG(DAC0_BASE_PTR,1)
#define DAC0_SR                                  DAC_SR_REG(DAC0_BASE_PTR)
#define DAC0_C0                                  DAC_C0_REG(DAC0_BASE_PTR)
#define DAC0_C1                                  DAC_C1_REG(DAC0_BASE_PTR)
#define DAC0_C2                                  DAC_C2_REG(DAC0_BASE_PTR)

/* DAC - Register array accessors */
#define DAC0_DATL(index)                         DAC_DATL_REG(DAC0_BASE_PTR,index)
#define DAC0_DATH(index)                         DAC_DATH_REG(DAC0_BASE_PTR,index)

/**
 * @}
 */ /* end of group DAC_Register_Accessor_Macros */


/**
 * @}
 */ /* end of group DAC_Peripheral */


/* ----------------------------------------------------------------------------
   -- DMA
   ---------------------------------------------------------------------------- */

/**
 * @addtogroup DMA_Peripheral DMA
 * @{
 */

/** DMA - Peripheral register structure */
typedef struct DMA_MemMap {
  uint8_t RESERVED_0[256];
  struct {                                         /* offset: 0x100, array step: 0x10 */
    uint32_t SAR;                                    /**< Source Address Register, array offset: 0x100, array step: 0x10 */
    uint32_t DAR;                                    /**< Destination Address Register, array offset: 0x104, array step: 0x10 */
    union {                                          /* offset: 0x108, array step: 0x10 */
      uint32_t DSR_BCR;                                /**< DMA Status Register / Byte Count Register, array offset: 0x108, array step: 0x10 */
      struct {                                         /* offset: 0x108, array step: 0x10 */
        uint8_t RESERVED_0[3];
        uint8_t DSR;                                     /**< DMA_DSR0 register...DMA_DSR3 register., array offset: 0x10B, array step: 0x10 */
      } DMA_DSR_ACCESS8BIT;
    };
    uint32_t DCR;                                    /**< DMA Control Register, array offset: 0x10C, array step: 0x10 */
  } DMA[4];
} volatile *DMA_MemMapPtr;

/* ----------------------------------------------------------------------------
   -- DMA - Register accessor macros
   ---------------------------------------------------------------------------- */

/**
 * @addtogroup DMA_Register_Accessor_Macros DMA - Register accessor macros
 * @{
 */


/* DMA - Register accessors */
#define DMA_SAR_REG(base,index)                  ((base)->DMA[index].SAR)
#define DMA_DAR_REG(base,index)                  ((base)->DMA[index].DAR)
#define DMA_DSR_BCR_REG(base,index)              ((base)->DMA[index].DSR_BCR)
#define DMA_DSR_REG(base,index)                  ((base)->DMA[index].DMA_DSR_ACCESS8BIT.DSR)
#define DMA_DCR_REG(base,index)                  ((base)->DMA[index].DCR)

/**
 * @}
 */ /* end of group DMA_Register_Accessor_Macros */


/* ----------------------------------------------------------------------------
   -- DMA Register Masks
   ---------------------------------------------------------------------------- */

/**
 * @addtogroup DMA_Register_Masks DMA Register Masks
 * @{
 */

/* SAR Bit Fields */
#define DMA_SAR_SAR_MASK                         0xFFFFFFFFu
#define DMA_SAR_SAR_SHIFT                        0
#define DMA_SAR_SAR(x)                           (((uint32_t)(((uint32_t)(x))<<DMA_SAR_SAR_SHIFT))&DMA_SAR_SAR_MASK)
/* DAR Bit Fields */
#define DMA_DAR_DAR_MASK                         0xFFFFFFFFu
#define DMA_DAR_DAR_SHIFT                        0
#define DMA_DAR_DAR(x)                           (((uint32_t)(((uint32_t)(x))<<DMA_DAR_DAR_SHIFT))&DMA_DAR_DAR_MASK)
/* DSR_BCR Bit Fields */
#define DMA_DSR_BCR_BCR_MASK                     0xFFFFFFu
#define DMA_DSR_BCR_BCR_SHIFT                    0
#define DMA_DSR_BCR_BCR(x)                       (((uint32_t)(((uint32_t)(x))<<DMA_DSR_BCR_BCR_SHIFT))&DMA_DSR_BCR_BCR_MASK)
#define DMA_DSR_BCR_DONE_MASK                    0x1000000u
#define DMA_DSR_BCR_DONE_SHIFT                   24
#define DMA_DSR_BCR_BSY_MASK                     0x2000000u
#define DMA_DSR_BCR_BSY_SHIFT                    25
#define DMA_DSR_BCR_REQ_MASK                     0x4000000u
#define DMA_DSR_BCR_REQ_SHIFT                    26
#define DMA_DSR_BCR_BED_MASK                     0x10000000u
#define DMA_DSR_BCR_BED_SHIFT                    28
#define DMA_DSR_BCR_BES_MASK                     0x20000000u
#define DMA_DSR_BCR_BES_SHIFT                    29
#define DMA_DSR_BCR_CE_MASK                      0x40000000u
#define DMA_DSR_BCR_CE_SHIFT                     30
/* DCR Bit Fields */
#define DMA_DCR_LCH2_MASK                        0x3u
#define DMA_DCR_LCH2_SHIFT                       0
#define DMA_DCR_LCH2(x)                          (((uint32_t)(((uint32_t)(x))<<DMA_DCR_LCH2_SHIFT))&DMA_DCR_LCH2_MASK)
#define DMA_DCR_LCH1_MASK                        0xCu
#define DMA_DCR_LCH1_SHIFT                       2
#define DMA_DCR_LCH1(x)                          (((uint32_t)(((uint32_t)(x))<<DMA_DCR_LCH1_SHIFT))&DMA_DCR_LCH1_MASK)
#define DMA_DCR_LINKCC_MASK                      0x30u
#define DMA_DCR_LINKCC_SHIFT                     4
#define DMA_DCR_LINKCC(x)                        (((uint32_t)(((uint32_t)(x))<<DMA_DCR_LINKCC_SHIFT))&DMA_DCR_LINKCC_MASK)
#define DMA_DCR_D_REQ_MASK                       0x80u
#define DMA_DCR_D_REQ_SHIFT                      7
#define DMA_DCR_DMOD_MASK                        0xF00u
#define DMA_DCR_DMOD_SHIFT                       8
#define DMA_DCR_DMOD(x)                          (((uint32_t)(((uint32_t)(x))<<DMA_DCR_DMOD_SHIFT))&DMA_DCR_DMOD_MASK)
#define DMA_DCR_SMOD_MASK                        0xF000u
#define DMA_DCR_SMOD_SHIFT                       12
#define DMA_DCR_SMOD(x)                          (((uint32_t)(((uint32_t)(x))<<DMA_DCR_SMOD_SHIFT))&DMA_DCR_SMOD_MASK)
#define DMA_DCR_START_MASK                       0x10000u
#define DMA_DCR_START_SHIFT                      16
#define DMA_DCR_DSIZE_MASK                       0x60000u
#define DMA_DCR_DSIZE_SHIFT                      17
#define DMA_DCR_DSIZE(x)                         (((uint32_t)(((uint32_t)(x))<<DMA_DCR_DSIZE_SHIFT))&DMA_DCR_DSIZE_MASK)
#define DMA_DCR_DINC_MASK                        0x80000u
#define DMA_DCR_DINC_SHIFT                       19
#define DMA_DCR_SSIZE_MASK                       0x300000u
#define DMA_DCR_SSIZE_SHIFT                      20
#define DMA_DCR_SSIZE(x)                         (((uint32_t)(((uint32_t)(x))<<DMA_DCR_SSIZE_SHIFT))&DMA_DCR_SSIZE_MASK)
#define DMA_DCR_SINC_MASK                        0x400000u
#define DMA_DCR_SINC_SHIFT                       22
#define DMA_DCR_EADREQ_MASK                      0x800000u
#define DMA_DCR_EADREQ_SHIFT                     23
#define DMA_DCR_AA_MASK                          0x10000000u
#define DMA_DCR_AA_SHIFT                         28
#define DMA_DCR_CS_MASK                          0x20000000u
#define DMA_DCR_CS_SHIFT                         29
#define DMA_DCR_ERQ_MASK                         0x40000000u
#define DMA_DCR_ERQ_SHIFT                        30
#define DMA_DCR_EINT_MASK                        0x80000000u
#define DMA_DCR_EINT_SHIFT                       31

/**
 * @}
 */ /* end of group DMA_Register_Masks */


/* DMA - Peripheral instance base addresses */
/** Peripheral DMA base pointer */
#define DMA_BASE_PTR                             ((DMA_MemMapPtr)0x40008000u)
/** Array initializer of DMA peripheral base pointers */
#define DMA_BASE_PTRS                            { DMA_BASE_PTR }

/* ----------------------------------------------------------------------------
   -- DMA - Register accessor macros
   ---------------------------------------------------------------------------- */

/**
 * @addtogroup DMA_Register_Accessor_Macros DMA - Register accessor macros
 * @{
 */


/* DMA - Register instance definitions */
/* DMA */
#define DMA_SAR0                                 DMA_SAR_REG(DMA_BASE_PTR,0)
#define DMA_DAR0                                 DMA_DAR_REG(DMA_BASE_PTR,0)
#define DMA_DSR_BCR0                             DMA_DSR_BCR_REG(DMA_BASE_PTR,0)
#define DMA_DSR0                                 DMA_DSR_REG(DMA_BASE_PTR,0)
#define DMA_DCR0                                 DMA_DCR_REG(DMA_BASE_PTR,0)
#define DMA_SAR1                                 DMA_SAR_REG(DMA_BASE_PTR,1)
#define DMA_DAR1                                 DMA_DAR_REG(DMA_BASE_PTR,1)
#define DMA_DSR_BCR1                             DMA_DSR_BCR_REG(DMA_BASE_PTR,1)
#define DMA_DSR1                                 DMA_DSR_REG(DMA_BASE_PTR,1)
#define DMA_DCR1                                 DMA_DCR_REG(DMA_BASE_PTR,1)
#define DMA_SAR2                                 DMA_SAR_REG(DMA_BASE_PTR,2)
#define DMA_DAR2                                 DMA_DAR_REG(DMA_BASE_PTR,2)
#define DMA_DSR_BCR2                             DMA_DSR_BCR_REG(DMA_BASE_PTR,2)
#define DMA_DSR2                                 DMA_DSR_REG(DMA_BASE_PTR,2)
#define DMA_DCR2                                 DMA_DCR_REG(DMA_BASE_PTR,2)
#define DMA_SAR3                                 DMA_SAR_REG(DMA_BASE_PTR,3)
#define DMA_DAR3                                 DMA_DAR_REG(DMA_BASE_PTR,3)
#define DMA_DSR_BCR3                             DMA_DSR_BCR_REG(DMA_BASE_PTR,3)
#define DMA_DSR3                                 DMA_DSR_REG(DMA_BASE_PTR,3)
#define DMA_DCR3                                 DMA_DCR_REG(DMA_BASE_PTR,3)

/* DMA - Register array accessors */
#define DMA_SAR(index)                           DMA_SAR_REG(DMA_BASE_PTR,index)
#define DMA_DAR(index)                           DMA_DAR_REG(DMA_BASE_PTR,index)
#define DMA_DSR_BCR(index)                       DMA_DSR_BCR_REG(DMA_BASE_PTR,index)
#define DMA_DSR(index)                           DMA_DSR_REG(DMA_BASE_PTR,index)
#define DMA_DCR(index)                           DMA_DCR_REG(DMA_BASE_PTR,index)

/**
 * @}
 */ /* end of group DMA_Register_Accessor_Macros */


/**
 * @}
 */ /* end of group DMA_Peripheral */


/* ----------------------------------------------------------------------------
   -- DMAMUX
   ---------------------------------------------------------------------------- */

/**
 * @addtogroup DMAMUX_Peripheral DMAMUX
 * @{
 */

/** DMAMUX - Peripheral register structure */
typedef struct DMAMUX_MemMap {
  uint8_t CHCFG[4];                                /**< Channel Configuration register, array offset: 0x0, array step: 0x1 */
} volatile *DMAMUX_MemMapPtr;

/* ----------------------------------------------------------------------------
   -- DMAMUX - Register accessor macros
   ---------------------------------------------------------------------------- */

/**
 * @addtogroup DMAMUX_Register_Accessor_Macros DMAMUX - Register accessor macros
 * @{
 */


/* DMAMUX - Register accessors */
#define DMAMUX_CHCFG_REG(base,index)             ((base)->CHCFG[index])

/**
 * @}
 */ /* end of group DMAMUX_Register_Accessor_Macros */


/* ----------------------------------------------------------------------------
   -- DMAMUX Register Masks
   ---------------------------------------------------------------------------- */

/**
 * @addtogroup DMAMUX_Register_Masks DMAMUX Register Masks
 * @{
 */

/* CHCFG Bit Fields */
#define DMAMUX_CHCFG_SOURCE_MASK                 0x3Fu
#define DMAMUX_CHCFG_SOURCE_SHIFT                0
#define DMAMUX_CHCFG_SOURCE(x)                   (((uint8_t)(((uint8_t)(x))<<DMAMUX_CHCFG_SOURCE_SHIFT))&DMAMUX_CHCFG_SOURCE_MASK)
#define DMAMUX_CHCFG_TRIG_MASK                   0x40u
#define DMAMUX_CHCFG_TRIG_SHIFT                  6
#define DMAMUX_CHCFG_ENBL_MASK                   0x80u
#define DMAMUX_CHCFG_ENBL_SHIFT                  7

/**
 * @}
 */ /* end of group DMAMUX_Register_Masks */


/* DMAMUX - Peripheral instance base addresses */
/** Peripheral DMAMUX0 base pointer */
#define DMAMUX0_BASE_PTR                         ((DMAMUX_MemMapPtr)0x40021000u)
/** Array initializer of DMAMUX peripheral base pointers */
#define DMAMUX_BASE_PTRS                         { DMAMUX0_BASE_PTR }

/* ----------------------------------------------------------------------------
   -- DMAMUX - Register accessor macros
   ---------------------------------------------------------------------------- */

/**
 * @addtogroup DMAMUX_Register_Accessor_Macros DMAMUX - Register accessor macros
 * @{
 */


/* DMAMUX - Register instance definitions */
/* DMAMUX0 */
#define DMAMUX0_CHCFG0                           DMAMUX_CHCFG_REG(DMAMUX0_BASE_PTR,0)
#define DMAMUX0_CHCFG1                           DMAMUX_CHCFG_REG(DMAMUX0_BASE_PTR,1)
#define DMAMUX0_CHCFG2                           DMAMUX_CHCFG_REG(DMAMUX0_BASE_PTR,2)
#define DMAMUX0_CHCFG3                           DMAMUX_CHCFG_REG(DMAMUX0_BASE_PTR,3)

/* DMAMUX - Register array accessors */
#define DMAMUX0_CHCFG(index)                     DMAMUX_CHCFG_REG(DMAMUX0_BASE_PTR,index)

/**
 * @}
 */ /* end of group DMAMUX_Register_Accessor_Macros */


/**
 * @}
 */ /* end of group DMAMUX_Peripheral */


/* ----------------------------------------------------------------------------
   -- DWT
   ---------------------------------------------------------------------------- */

/**
 * @addtogroup DWT_Peripheral DWT
 * @{
 */

/** DWT - Peripheral register structure */
typedef struct DWT_MemMap {
  uint32_t CTRL;                                   /**< Control Register, offset: 0x0 */
  uint8_t RESERVED_0[24];
  uint32_t PCSR;                                   /**< Program Counter Sample Register, offset: 0x1C */
  struct {                                         /* offset: 0x20, array step: 0x10 */
    uint32_t COMP;                                   /**< Comparator Register 0..Comparator Register 1, array offset: 0x20, array step: 0x10 */
    uint32_t MASK;                                   /**< Mask Register 0..Mask Register 1, array offset: 0x24, array step: 0x10 */
    uint32_t FUNCTION;                               /**< Function Register 0..Function Register 1, array offset: 0x28, array step: 0x10 */
    uint8_t RESERVED_0[4];
  } COMPARATOR[2];
} volatile *DWT_MemMapPtr;

/* ----------------------------------------------------------------------------
   -- DWT - Register accessor macros
   ---------------------------------------------------------------------------- */

/**
 * @addtogroup DWT_Register_Accessor_Macros DWT - Register accessor macros
 * @{
 */


/* DWT - Register accessors */
#define DWT_CTRL_REG(base)                       ((base)->CTRL)
#define DWT_PCSR_REG(base)                       ((base)->PCSR)
#define DWT_COMP_REG(base,index)                 ((base)->COMPARATOR[index].COMP)
#define DWT_MASK_REG(base,index)                 ((base)->COMPARATOR[index].MASK)
#define DWT_FUNCTION_REG(base,index)             ((base)->COMPARATOR[index].FUNCTION)

/**
 * @}
 */ /* end of group DWT_Register_Accessor_Macros */


/* ----------------------------------------------------------------------------
   -- DWT Register Masks
   ---------------------------------------------------------------------------- */

/**
 * @addtogroup DWT_Register_Masks DWT Register Masks
 * @{
 */


/**
 * @}
 */ /* end of group DWT_Register_Masks */


/* DWT - Peripheral instance base addresses */
/** Peripheral DWT base pointer */
#define DWT_BASE_PTR                             ((DWT_MemMapPtr)0xE0001000u)
/** Array initializer of DWT peripheral base pointers */
#define DWT_BASE_PTRS                            { DWT_BASE_PTR }

/* ----------------------------------------------------------------------------
   -- DWT - Register accessor macros
   ---------------------------------------------------------------------------- */

/**
 * @addtogroup DWT_Register_Accessor_Macros DWT - Register accessor macros
 * @{
 */


/* DWT - Register instance definitions */
/* DWT */
#define DWT_CTRL                                 DWT_CTRL_REG(DWT_BASE_PTR)
#define DWT_PCSR                                 DWT_PCSR_REG(DWT_BASE_PTR)
#define DWT_COMP0                                DWT_COMP_REG(DWT_BASE_PTR,0)
#define DWT_MASK0                                DWT_MASK_REG(DWT_BASE_PTR,0)
#define DWT_FUNCTION0                            DWT_FUNCTION_REG(DWT_BASE_PTR,0)
#define DWT_COMP1                                DWT_COMP_REG(DWT_BASE_PTR,1)
#define DWT_MASK1                                DWT_MASK_REG(DWT_BASE_PTR,1)
#define DWT_FUNCTION1                            DWT_FUNCTION_REG(DWT_BASE_PTR,1)

/* DWT - Register array accessors */
#define DWT_COMP(index)                          DWT_COMP_REG(DWT_BASE_PTR,index)
#define DWT_MASK(index)                          DWT_MASK_REG(DWT_BASE_PTR,index)
#define DWT_FUNCTION(index)                      DWT_FUNCTION_REG(DWT_BASE_PTR,index)

/**
 * @}
 */ /* end of group DWT_Register_Accessor_Macros */


/**
 * @}
 */ /* end of group DWT_Peripheral */


/* ----------------------------------------------------------------------------
   -- FGPIO
   ---------------------------------------------------------------------------- */

/**
 * @addtogroup FGPIO_Peripheral FGPIO
 * @{
 */

/** FGPIO - Peripheral register structure */
typedef struct FGPIO_MemMap {
  uint32_t PDOR;                                   /**< Port Data Output Register, offset: 0x0 */
  uint32_t PSOR;                                   /**< Port Set Output Register, offset: 0x4 */
  uint32_t PCOR;                                   /**< Port Clear Output Register, offset: 0x8 */
  uint32_t PTOR;                                   /**< Port Toggle Output Register, offset: 0xC */
  uint32_t PDIR;                                   /**< Port Data Input Register, offset: 0x10 */
  uint32_t PDDR;                                   /**< Port Data Direction Register, offset: 0x14 */
} volatile *FGPIO_MemMapPtr;

/* ----------------------------------------------------------------------------
   -- FGPIO - Register accessor macros
   ---------------------------------------------------------------------------- */

/**
 * @addtogroup FGPIO_Register_Accessor_Macros FGPIO - Register accessor macros
 * @{
 */


/* FGPIO - Register accessors */
#define FGPIO_PDOR_REG(base)                     ((base)->PDOR)
#define FGPIO_PSOR_REG(base)                     ((base)->PSOR)
#define FGPIO_PCOR_REG(base)                     ((base)->PCOR)
#define FGPIO_PTOR_REG(base)                     ((base)->PTOR)
#define FGPIO_PDIR_REG(base)                     ((base)->PDIR)
#define FGPIO_PDDR_REG(base)                     ((base)->PDDR)

/**
 * @}
 */ /* end of group FGPIO_Register_Accessor_Macros */


/* ----------------------------------------------------------------------------
   -- FGPIO Register Masks
   ---------------------------------------------------------------------------- */

/**
 * @addtogroup FGPIO_Register_Masks FGPIO Register Masks
 * @{
 */

/* PDOR Bit Fields */
#define FGPIO_PDOR_PDO_MASK                      0xFFFFFFFFu
#define FGPIO_PDOR_PDO_SHIFT                     0
#define FGPIO_PDOR_PDO(x)                        (((uint32_t)(((uint32_t)(x))<<FGPIO_PDOR_PDO_SHIFT))&FGPIO_PDOR_PDO_MASK)
/* PSOR Bit Fields */
#define FGPIO_PSOR_PTSO_MASK                     0xFFFFFFFFu
#define FGPIO_PSOR_PTSO_SHIFT                    0
#define FGPIO_PSOR_PTSO(x)                       (((uint32_t)(((uint32_t)(x))<<FGPIO_PSOR_PTSO_SHIFT))&FGPIO_PSOR_PTSO_MASK)
/* PCOR Bit Fields */
#define FGPIO_PCOR_PTCO_MASK                     0xFFFFFFFFu
#define FGPIO_PCOR_PTCO_SHIFT                    0
#define FGPIO_PCOR_PTCO(x)                       (((uint32_t)(((uint32_t)(x))<<FGPIO_PCOR_PTCO_SHIFT))&FGPIO_PCOR_PTCO_MASK)
/* PTOR Bit Fields */
#define FGPIO_PTOR_PTTO_MASK                     0xFFFFFFFFu
#define FGPIO_PTOR_PTTO_SHIFT                    0
#define FGPIO_PTOR_PTTO(x)                       (((uint32_t)(((uint32_t)(x))<<FGPIO_PTOR_PTTO_SHIFT))&FGPIO_PTOR_PTTO_MASK)
/* PDIR Bit Fields */
#define FGPIO_PDIR_PDI_MASK                      0xFFFFFFFFu
#define FGPIO_PDIR_PDI_SHIFT                     0
#define FGPIO_PDIR_PDI(x)                        (((uint32_t)(((uint32_t)(x))<<FGPIO_PDIR_PDI_SHIFT))&FGPIO_PDIR_PDI_MASK)
/* PDDR Bit Fields */
#define FGPIO_PDDR_PDD_MASK                      0xFFFFFFFFu
#define FGPIO_PDDR_PDD_SHIFT                     0
#define FGPIO_PDDR_PDD(x)                        (((uint32_t)(((uint32_t)(x))<<FGPIO_PDDR_PDD_SHIFT))&FGPIO_PDDR_PDD_MASK)

/**
 * @}
 */ /* end of group FGPIO_Register_Masks */


/* FGPIO - Peripheral instance base addresses */
/** Peripheral FPTA base pointer */
#define FPTA_BASE_PTR                            ((FGPIO_MemMapPtr)0xF80FF000u)
/** Peripheral FPTB base pointer */
#define FPTB_BASE_PTR                            ((FGPIO_MemMapPtr)0xF80FF040u)
/** Peripheral FPTC base pointer */
#define FPTC_BASE_PTR                            ((FGPIO_MemMapPtr)0xF80FF080u)
/** Peripheral FPTD base pointer */
#define FPTD_BASE_PTR                            ((FGPIO_MemMapPtr)0xF80FF0C0u)
/** Peripheral FPTE base pointer */
#define FPTE_BASE_PTR                            ((FGPIO_MemMapPtr)0xF80FF100u)
/** Array initializer of FGPIO peripheral base pointers */
#define FGPIO_BASE_PTRS                          { FPTA_BASE_PTR, FPTB_BASE_PTR, FPTC_BASE_PTR, FPTD_BASE_PTR, FPTE_BASE_PTR }

/* ----------------------------------------------------------------------------
   -- FGPIO - Register accessor macros
   ---------------------------------------------------------------------------- */

/**
 * @addtogroup FGPIO_Register_Accessor_Macros FGPIO - Register accessor macros
 * @{
 */


/* FGPIO - Register instance definitions */
/* FPTA */
#define FGPIOA_PDOR                              FGPIO_PDOR_REG(FPTA_BASE_PTR)
#define FGPIOA_PSOR                              FGPIO_PSOR_REG(FPTA_BASE_PTR)
#define FGPIOA_PCOR                              FGPIO_PCOR_REG(FPTA_BASE_PTR)
#define FGPIOA_PTOR                              FGPIO_PTOR_REG(FPTA_BASE_PTR)
#define FGPIOA_PDIR                              FGPIO_PDIR_REG(FPTA_BASE_PTR)
#define FGPIOA_PDDR                              FGPIO_PDDR_REG(FPTA_BASE_PTR)
/* FPTB */
#define FGPIOB_PDOR                              FGPIO_PDOR_REG(FPTB_BASE_PTR)
#define FGPIOB_PSOR                              FGPIO_PSOR_REG(FPTB_BASE_PTR)
#define FGPIOB_PCOR                              FGPIO_PCOR_REG(FPTB_BASE_PTR)
#define FGPIOB_PTOR                              FGPIO_PTOR_REG(FPTB_BASE_PTR)
#define FGPIOB_PDIR                              FGPIO_PDIR_REG(FPTB_BASE_PTR)
#define FGPIOB_PDDR                              FGPIO_PDDR_REG(FPTB_BASE_PTR)
/* FPTC */
#define FGPIOC_PDOR                              FGPIO_PDOR_REG(FPTC_BASE_PTR)
#define FGPIOC_PSOR                              FGPIO_PSOR_REG(FPTC_BASE_PTR)
#define FGPIOC_PCOR                              FGPIO_PCOR_REG(FPTC_BASE_PTR)
#define FGPIOC_PTOR                              FGPIO_PTOR_REG(FPTC_BASE_PTR)
#define FGPIOC_PDIR                              FGPIO_PDIR_REG(FPTC_BASE_PTR)
#define FGPIOC_PDDR                              FGPIO_PDDR_REG(FPTC_BASE_PTR)
/* FPTD */
#define FGPIOD_PDOR                              FGPIO_PDOR_REG(FPTD_BASE_PTR)
#define FGPIOD_PSOR                              FGPIO_PSOR_REG(FPTD_BASE_PTR)
#define FGPIOD_PCOR                              FGPIO_PCOR_REG(FPTD_BASE_PTR)
#define FGPIOD_PTOR                              FGPIO_PTOR_REG(FPTD_BASE_PTR)
#define FGPIOD_PDIR                              FGPIO_PDIR_REG(FPTD_BASE_PTR)
#define FGPIOD_PDDR                              FGPIO_PDDR_REG(FPTD_BASE_PTR)
/* FPTE */
#define FGPIOE_PDOR                              FGPIO_PDOR_REG(FPTE_BASE_PTR)
#define FGPIOE_PSOR                              FGPIO_PSOR_REG(FPTE_BASE_PTR)
#define FGPIOE_PCOR                              FGPIO_PCOR_REG(FPTE_BASE_PTR)
#define FGPIOE_PTOR                              FGPIO_PTOR_REG(FPTE_BASE_PTR)
#define FGPIOE_PDIR                              FGPIO_PDIR_REG(FPTE_BASE_PTR)
#define FGPIOE_PDDR                              FGPIO_PDDR_REG(FPTE_BASE_PTR)

/**
 * @}
 */ /* end of group FGPIO_Register_Accessor_Macros */


/**
 * @}
 */ /* end of group FGPIO_Peripheral */


/* ----------------------------------------------------------------------------
   -- FTFA
   ---------------------------------------------------------------------------- */

/**
 * @addtogroup FTFA_Peripheral FTFA
 * @{
 */

/** FTFA - Peripheral register structure */
typedef struct FTFA_MemMap {
  uint8_t FSTAT;                                   /**< Flash Status Register, offset: 0x0 */
  uint8_t FCNFG;                                   /**< Flash Configuration Register, offset: 0x1 */
  uint8_t FSEC;                                    /**< Flash Security Register, offset: 0x2 */
  uint8_t FOPT;                                    /**< Flash Option Register, offset: 0x3 */
  uint8_t FCCOB3;                                  /**< Flash Common Command Object Registers, offset: 0x4 */
  uint8_t FCCOB2;                                  /**< Flash Common Command Object Registers, offset: 0x5 */
  uint8_t FCCOB1;                                  /**< Flash Common Command Object Registers, offset: 0x6 */
  uint8_t FCCOB0;                                  /**< Flash Common Command Object Registers, offset: 0x7 */
  uint8_t FCCOB7;                                  /**< Flash Common Command Object Registers, offset: 0x8 */
  uint8_t FCCOB6;                                  /**< Flash Common Command Object Registers, offset: 0x9 */
  uint8_t FCCOB5;                                  /**< Flash Common Command Object Registers, offset: 0xA */
  uint8_t FCCOB4;                                  /**< Flash Common Command Object Registers, offset: 0xB */
  uint8_t FCCOBB;                                  /**< Flash Common Command Object Registers, offset: 0xC */
  uint8_t FCCOBA;                                  /**< Flash Common Command Object Registers, offset: 0xD */
  uint8_t FCCOB9;                                  /**< Flash Common Command Object Registers, offset: 0xE */
  uint8_t FCCOB8;                                  /**< Flash Common Command Object Registers, offset: 0xF */
  uint8_t FPROT3;                                  /**< Program Flash Protection Registers, offset: 0x10 */
  uint8_t FPROT2;                                  /**< Program Flash Protection Registers, offset: 0x11 */
  uint8_t FPROT1;                                  /**< Program Flash Protection Registers, offset: 0x12 */
  uint8_t FPROT0;                                  /**< Program Flash Protection Registers, offset: 0x13 */
} volatile *FTFA_MemMapPtr;

/* ----------------------------------------------------------------------------
   -- FTFA - Register accessor macros
   ---------------------------------------------------------------------------- */

/**
 * @addtogroup FTFA_Register_Accessor_Macros FTFA - Register accessor macros
 * @{
 */


/* FTFA - Register accessors */
#define FTFA_FSTAT_REG(base)                     ((base)->FSTAT)
#define FTFA_FCNFG_REG(base)                     ((base)->FCNFG)
#define FTFA_FSEC_REG(base)                      ((base)->FSEC)
#define FTFA_FOPT_REG(base)                      ((base)->FOPT)
#define FTFA_FCCOB3_REG(base)                    ((base)->FCCOB3)
#define FTFA_FCCOB2_REG(base)                    ((base)->FCCOB2)
#define FTFA_FCCOB1_REG(base)                    ((base)->FCCOB1)
#define FTFA_FCCOB0_REG(base)                    ((base)->FCCOB0)
#define FTFA_FCCOB7_REG(base)                    ((base)->FCCOB7)
#define FTFA_FCCOB6_REG(base)                    ((base)->FCCOB6)
#define FTFA_FCCOB5_REG(base)                    ((base)->FCCOB5)
#define FTFA_FCCOB4_REG(base)                    ((base)->FCCOB4)
#define FTFA_FCCOBB_REG(base)                    ((base)->FCCOBB)
#define FTFA_FCCOBA_REG(base)                    ((base)->FCCOBA)
#define FTFA_FCCOB9_REG(base)                    ((base)->FCCOB9)
#define FTFA_FCCOB8_REG(base)                    ((base)->FCCOB8)
#define FTFA_FPROT3_REG(base)                    ((base)->FPROT3)
#define FTFA_FPROT2_REG(base)                    ((base)->FPROT2)
#define FTFA_FPROT1_REG(base)                    ((base)->FPROT1)
#define FTFA_FPROT0_REG(base)                    ((base)->FPROT0)

/**
 * @}
 */ /* end of group FTFA_Register_Accessor_Macros */


/* ----------------------------------------------------------------------------
   -- FTFA Register Masks
   ---------------------------------------------------------------------------- */

/**
 * @addtogroup FTFA_Register_Masks FTFA Register Masks
 * @{
 */

/* FSTAT Bit Fields */
#define FTFA_FSTAT_MGSTAT0_MASK                  0x1u
#define FTFA_FSTAT_MGSTAT0_SHIFT                 0
#define FTFA_FSTAT_FPVIOL_MASK                   0x10u
#define FTFA_FSTAT_FPVIOL_SHIFT                  4
#define FTFA_FSTAT_ACCERR_MASK                   0x20u
#define FTFA_FSTAT_ACCERR_SHIFT                  5
#define FTFA_FSTAT_RDCOLERR_MASK                 0x40u
#define FTFA_FSTAT_RDCOLERR_SHIFT                6
#define FTFA_FSTAT_CCIF_MASK                     0x80u
#define FTFA_FSTAT_CCIF_SHIFT                    7
/* FCNFG Bit Fields */
#define FTFA_FCNFG_ERSSUSP_MASK                  0x10u
#define FTFA_FCNFG_ERSSUSP_SHIFT                 4
#define FTFA_FCNFG_ERSAREQ_MASK                  0x20u
#define FTFA_FCNFG_ERSAREQ_SHIFT                 5
#define FTFA_FCNFG_RDCOLLIE_MASK                 0x40u
#define FTFA_FCNFG_RDCOLLIE_SHIFT                6
#define FTFA_FCNFG_CCIE_MASK                     0x80u
#define FTFA_FCNFG_CCIE_SHIFT                    7
/* FSEC Bit Fields */
#define FTFA_FSEC_SEC_MASK                       0x3u
#define FTFA_FSEC_SEC_SHIFT                      0
#define FTFA_FSEC_SEC(x)                         (((uint8_t)(((uint8_t)(x))<<FTFA_FSEC_SEC_SHIFT))&FTFA_FSEC_SEC_MASK)
#define FTFA_FSEC_FSLACC_MASK                    0xCu
#define FTFA_FSEC_FSLACC_SHIFT                   2
#define FTFA_FSEC_FSLACC(x)                      (((uint8_t)(((uint8_t)(x))<<FTFA_FSEC_FSLACC_SHIFT))&FTFA_FSEC_FSLACC_MASK)
#define FTFA_FSEC_MEEN_MASK                      0x30u
#define FTFA_FSEC_MEEN_SHIFT                     4
#define FTFA_FSEC_MEEN(x)                        (((uint8_t)(((uint8_t)(x))<<FTFA_FSEC_MEEN_SHIFT))&FTFA_FSEC_MEEN_MASK)
#define FTFA_FSEC_KEYEN_MASK                     0xC0u
#define FTFA_FSEC_KEYEN_SHIFT                    6
#define FTFA_FSEC_KEYEN(x)                       (((uint8_t)(((uint8_t)(x))<<FTFA_FSEC_KEYEN_SHIFT))&FTFA_FSEC_KEYEN_MASK)
/* FOPT Bit Fields */
#define FTFA_FOPT_OPT_MASK                       0xFFu
#define FTFA_FOPT_OPT_SHIFT                      0
#define FTFA_FOPT_OPT(x)                         (((uint8_t)(((uint8_t)(x))<<FTFA_FOPT_OPT_SHIFT))&FTFA_FOPT_OPT_MASK)
/* FCCOB3 Bit Fields */
#define FTFA_FCCOB3_CCOBn_MASK                   0xFFu
#define FTFA_FCCOB3_CCOBn_SHIFT                  0
#define FTFA_FCCOB3_CCOBn(x)                     (((uint8_t)(((uint8_t)(x))<<FTFA_FCCOB3_CCOBn_SHIFT))&FTFA_FCCOB3_CCOBn_MASK)
/* FCCOB2 Bit Fields */
#define FTFA_FCCOB2_CCOBn_MASK                   0xFFu
#define FTFA_FCCOB2_CCOBn_SHIFT                  0
#define FTFA_FCCOB2_CCOBn(x)                     (((uint8_t)(((uint8_t)(x))<<FTFA_FCCOB2_CCOBn_SHIFT))&FTFA_FCCOB2_CCOBn_MASK)
/* FCCOB1 Bit Fields */
#define FTFA_FCCOB1_CCOBn_MASK                   0xFFu
#define FTFA_FCCOB1_CCOBn_SHIFT                  0
#define FTFA_FCCOB1_CCOBn(x)                     (((uint8_t)(((uint8_t)(x))<<FTFA_FCCOB1_CCOBn_SHIFT))&FTFA_FCCOB1_CCOBn_MASK)
/* FCCOB0 Bit Fields */
#define FTFA_FCCOB0_CCOBn_MASK                   0xFFu
#define FTFA_FCCOB0_CCOBn_SHIFT                  0
#define FTFA_FCCOB0_CCOBn(x)                     (((uint8_t)(((uint8_t)(x))<<FTFA_FCCOB0_CCOBn_SHIFT))&FTFA_FCCOB0_CCOBn_MASK)
/* FCCOB7 Bit Fields */
#define FTFA_FCCOB7_CCOBn_MASK                   0xFFu
#define FTFA_FCCOB7_CCOBn_SHIFT                  0
#define FTFA_FCCOB7_CCOBn(x)                     (((uint8_t)(((uint8_t)(x))<<FTFA_FCCOB7_CCOBn_SHIFT))&FTFA_FCCOB7_CCOBn_MASK)
/* FCCOB6 Bit Fields */
#define FTFA_FCCOB6_CCOBn_MASK                   0xFFu
#define FTFA_FCCOB6_CCOBn_SHIFT                  0
#define FTFA_FCCOB6_CCOBn(x)                     (((uint8_t)(((uint8_t)(x))<<FTFA_FCCOB6_CCOBn_SHIFT))&FTFA_FCCOB6_CCOBn_MASK)
/* FCCOB5 Bit Fields */
#define FTFA_FCCOB5_CCOBn_MASK                   0xFFu
#define FTFA_FCCOB5_CCOBn_SHIFT                  0
#define FTFA_FCCOB5_CCOBn(x)                     (((uint8_t)(((uint8_t)(x))<<FTFA_FCCOB5_CCOBn_SHIFT))&FTFA_FCCOB5_CCOBn_MASK)
/* FCCOB4 Bit Fields */
#define FTFA_FCCOB4_CCOBn_MASK                   0xFFu
#define FTFA_FCCOB4_CCOBn_SHIFT                  0
#define FTFA_FCCOB4_CCOBn(x)                     (((uint8_t)(((uint8_t)(x))<<FTFA_FCCOB4_CCOBn_SHIFT))&FTFA_FCCOB4_CCOBn_MASK)
/* FCCOBB Bit Fields */
#define FTFA_FCCOBB_CCOBn_MASK                   0xFFu
#define FTFA_FCCOBB_CCOBn_SHIFT                  0
#define FTFA_FCCOBB_CCOBn(x)                     (((uint8_t)(((uint8_t)(x))<<FTFA_FCCOBB_CCOBn_SHIFT))&FTFA_FCCOBB_CCOBn_MASK)
/* FCCOBA Bit Fields */
#define FTFA_FCCOBA_CCOBn_MASK                   0xFFu
#define FTFA_FCCOBA_CCOBn_SHIFT                  0
#define FTFA_FCCOBA_CCOBn(x)                     (((uint8_t)(((uint8_t)(x))<<FTFA_FCCOBA_CCOBn_SHIFT))&FTFA_FCCOBA_CCOBn_MASK)
/* FCCOB9 Bit Fields */
#define FTFA_FCCOB9_CCOBn_MASK                   0xFFu
#define FTFA_FCCOB9_CCOBn_SHIFT                  0
#define FTFA_FCCOB9_CCOBn(x)                     (((uint8_t)(((uint8_t)(x))<<FTFA_FCCOB9_CCOBn_SHIFT))&FTFA_FCCOB9_CCOBn_MASK)
/* FCCOB8 Bit Fields */
#define FTFA_FCCOB8_CCOBn_MASK                   0xFFu
#define FTFA_FCCOB8_CCOBn_SHIFT                  0
#define FTFA_FCCOB8_CCOBn(x)                     (((uint8_t)(((uint8_t)(x))<<FTFA_FCCOB8_CCOBn_SHIFT))&FTFA_FCCOB8_CCOBn_MASK)
/* FPROT3 Bit Fields */
#define FTFA_FPROT3_PROT_MASK                    0xFFu
#define FTFA_FPROT3_PROT_SHIFT                   0
#define FTFA_FPROT3_PROT(x)                      (((uint8_t)(((uint8_t)(x))<<FTFA_FPROT3_PROT_SHIFT))&FTFA_FPROT3_PROT_MASK)
/* FPROT2 Bit Fields */
#define FTFA_FPROT2_PROT_MASK                    0xFFu
#define FTFA_FPROT2_PROT_SHIFT                   0
#define FTFA_FPROT2_PROT(x)                      (((uint8_t)(((uint8_t)(x))<<FTFA_FPROT2_PROT_SHIFT))&FTFA_FPROT2_PROT_MASK)
/* FPROT1 Bit Fields */
#define FTFA_FPROT1_PROT_MASK                    0xFFu
#define FTFA_FPROT1_PROT_SHIFT                   0
#define FTFA_FPROT1_PROT(x)                      (((uint8_t)(((uint8_t)(x))<<FTFA_FPROT1_PROT_SHIFT))&FTFA_FPROT1_PROT_MASK)
/* FPROT0 Bit Fields */
#define FTFA_FPROT0_PROT_MASK                    0xFFu
#define FTFA_FPROT0_PROT_SHIFT                   0
#define FTFA_FPROT0_PROT(x)                      (((uint8_t)(((uint8_t)(x))<<FTFA_FPROT0_PROT_SHIFT))&FTFA_FPROT0_PROT_MASK)

/**
 * @}
 */ /* end of group FTFA_Register_Masks */


/* FTFA - Peripheral instance base addresses */
/** Peripheral FTFA base pointer */
#define FTFA_BASE_PTR                            ((FTFA_MemMapPtr)0x40020000u)
/** Array initializer of FTFA peripheral base pointers */
#define FTFA_BASE_PTRS                           { FTFA_BASE_PTR }

/* ----------------------------------------------------------------------------
   -- FTFA - Register accessor macros
   ---------------------------------------------------------------------------- */

/**
 * @addtogroup FTFA_Register_Accessor_Macros FTFA - Register accessor macros
 * @{
 */


/* FTFA - Register instance definitions */
/* FTFA */
#define FTFA_FSTAT                               FTFA_FSTAT_REG(FTFA_BASE_PTR)
#define FTFA_FCNFG                               FTFA_FCNFG_REG(FTFA_BASE_PTR)
#define FTFA_FSEC                                FTFA_FSEC_REG(FTFA_BASE_PTR)
#define FTFA_FOPT                                FTFA_FOPT_REG(FTFA_BASE_PTR)
#define FTFA_FCCOB3                              FTFA_FCCOB3_REG(FTFA_BASE_PTR)
#define FTFA_FCCOB2                              FTFA_FCCOB2_REG(FTFA_BASE_PTR)
#define FTFA_FCCOB1                              FTFA_FCCOB1_REG(FTFA_BASE_PTR)
#define FTFA_FCCOB0                              FTFA_FCCOB0_REG(FTFA_BASE_PTR)
#define FTFA_FCCOB7                              FTFA_FCCOB7_REG(FTFA_BASE_PTR)
#define FTFA_FCCOB6                              FTFA_FCCOB6_REG(FTFA_BASE_PTR)
#define FTFA_FCCOB5                              FTFA_FCCOB5_REG(FTFA_BASE_PTR)
#define FTFA_FCCOB4                              FTFA_FCCOB4_REG(FTFA_BASE_PTR)
#define FTFA_FCCOBB                              FTFA_FCCOBB_REG(FTFA_BASE_PTR)
#define FTFA_FCCOBA                              FTFA_FCCOBA_REG(FTFA_BASE_PTR)
#define FTFA_FCCOB9                              FTFA_FCCOB9_REG(FTFA_BASE_PTR)
#define FTFA_FCCOB8                              FTFA_FCCOB8_REG(FTFA_BASE_PTR)
#define FTFA_FPROT3                              FTFA_FPROT3_REG(FTFA_BASE_PTR)
#define FTFA_FPROT2                              FTFA_FPROT2_REG(FTFA_BASE_PTR)
#define FTFA_FPROT1                              FTFA_FPROT1_REG(FTFA_BASE_PTR)
#define FTFA_FPROT0                              FTFA_FPROT0_REG(FTFA_BASE_PTR)

/**
 * @}
 */ /* end of group FTFA_Register_Accessor_Macros */


/**
 * @}
 */ /* end of group FTFA_Peripheral */


/* ----------------------------------------------------------------------------
   -- GPIO
   ---------------------------------------------------------------------------- */

/**
 * @addtogroup GPIO_Peripheral GPIO
 * @{
 */

/** GPIO - Peripheral register structure */
typedef struct GPIO_MemMap {
  uint32_t PDOR;                                   /**< Port Data Output Register, offset: 0x0 */
  uint32_t PSOR;                                   /**< Port Set Output Register, offset: 0x4 */
  uint32_t PCOR;                                   /**< Port Clear Output Register, offset: 0x8 */
  uint32_t PTOR;                                   /**< Port Toggle Output Register, offset: 0xC */
  uint32_t PDIR;                                   /**< Port Data Input Register, offset: 0x10 */
  uint32_t PDDR;                                   /**< Port Data Direction Register, offset: 0x14 */
} volatile *GPIO_MemMapPtr;

/* ----------------------------------------------------------------------------
   -- GPIO - Register accessor macros
   ---------------------------------------------------------------------------- */

/**
 * @addtogroup GPIO_Register_Accessor_Macros GPIO - Register accessor macros
 * @{
 */


/* GPIO - Register accessors */
#define GPIO_PDOR_REG(base)                      ((base)->PDOR)
#define GPIO_PSOR_REG(base)                      ((base)->PSOR)
#define GPIO_PCOR_REG(base)                      ((base)->PCOR)
#define GPIO_PTOR_REG(base)                      ((base)->PTOR)
#define GPIO_PDIR_REG(base)                      ((base)->PDIR)
#define GPIO_PDDR_REG(base)                      ((base)->PDDR)

/**
 * @}
 */ /* end of group GPIO_Register_Accessor_Macros */


/* ----------------------------------------------------------------------------
   -- GPIO Register Masks
   ---------------------------------------------------------------------------- */

/**
 * @addtogroup GPIO_Register_Masks GPIO Register Masks
 * @{
 */

/* PDOR Bit Fields */
#define GPIO_PDOR_PDO_MASK                       0xFFFFFFFFu
#define GPIO_PDOR_PDO_SHIFT                      0
#define GPIO_PDOR_PDO(x)                         (((uint32_t)(((uint32_t)(x))<<GPIO_PDOR_PDO_SHIFT))&GPIO_PDOR_PDO_MASK)
/* PSOR Bit Fields */
#define GPIO_PSOR_PTSO_MASK                      0xFFFFFFFFu
#define GPIO_PSOR_PTSO_SHIFT                     0
#define GPIO_PSOR_PTSO(x)                        (((uint32_t)(((uint32_t)(x))<<GPIO_PSOR_PTSO_SHIFT))&GPIO_PSOR_PTSO_MASK)
/* PCOR Bit Fields */
#define GPIO_PCOR_PTCO_MASK                      0xFFFFFFFFu
#define GPIO_PCOR_PTCO_SHIFT                     0
#define GPIO_PCOR_PTCO(x)                        (((uint32_t)(((uint32_t)(x))<<GPIO_PCOR_PTCO_SHIFT))&GPIO_PCOR_PTCO_MASK)
/* PTOR Bit Fields */
#define GPIO_PTOR_PTTO_MASK                      0xFFFFFFFFu
#define GPIO_PTOR_PTTO_SHIFT                     0
#define GPIO_PTOR_PTTO(x)                        (((uint32_t)(((uint32_t)(x))<<GPIO_PTOR_PTTO_SHIFT))&GPIO_PTOR_PTTO_MASK)
/* PDIR Bit Fields */
#define GPIO_PDIR_PDI_MASK                       0xFFFFFFFFu
#define GPIO_PDIR_PDI_SHIFT                      0
#define GPIO_PDIR_PDI(x)                         (((uint32_t)(((uint32_t)(x))<<GPIO_PDIR_PDI_SHIFT))&GPIO_PDIR_PDI_MASK)
/* PDDR Bit Fields */
#define GPIO_PDDR_PDD_MASK                       0xFFFFFFFFu
#define GPIO_PDDR_PDD_SHIFT                      0
#define GPIO_PDDR_PDD(x)                         (((uint32_t)(((uint32_t)(x))<<GPIO_PDDR_PDD_SHIFT))&GPIO_PDDR_PDD_MASK)

/**
 * @}
 */ /* end of group GPIO_Register_Masks */


/* GPIO - Peripheral instance base addresses */
/** Peripheral PTA base pointer */
#define PTA_BASE_PTR                             ((GPIO_MemMapPtr)0x400FF000u)
/** Peripheral PTB base pointer */
#define PTB_BASE_PTR                             ((GPIO_MemMapPtr)0x400FF040u)
/** Peripheral PTC base pointer */
#define PTC_BASE_PTR                             ((GPIO_MemMapPtr)0x400FF080u)
/** Peripheral PTD base pointer */
#define PTD_BASE_PTR                             ((GPIO_MemMapPtr)0x400FF0C0u)
/** Peripheral PTE base pointer */
#define PTE_BASE_PTR                             ((GPIO_MemMapPtr)0x400FF100u)
/** Array initializer of GPIO peripheral base pointers */
#define GPIO_BASE_PTRS                           { PTA_BASE_PTR, PTB_BASE_PTR, PTC_BASE_PTR, PTD_BASE_PTR, PTE_BASE_PTR }

/* ----------------------------------------------------------------------------
   -- GPIO - Register accessor macros
   ---------------------------------------------------------------------------- */

/**
 * @addtogroup GPIO_Register_Accessor_Macros GPIO - Register accessor macros
 * @{
 */


/* GPIO - Register instance definitions */
/* PTA */
#define GPIOA_PDOR                               GPIO_PDOR_REG(PTA_BASE_PTR)
#define GPIOA_PSOR                               GPIO_PSOR_REG(PTA_BASE_PTR)
#define GPIOA_PCOR                               GPIO_PCOR_REG(PTA_BASE_PTR)
#define GPIOA_PTOR                               GPIO_PTOR_REG(PTA_BASE_PTR)
#define GPIOA_PDIR                               GPIO_PDIR_REG(PTA_BASE_PTR)
#define GPIOA_PDDR                               GPIO_PDDR_REG(PTA_BASE_PTR)
/* PTB */
#define GPIOB_PDOR                               GPIO_PDOR_REG(PTB_BASE_PTR)
#define GPIOB_PSOR                               GPIO_PSOR_REG(PTB_BASE_PTR)
#define GPIOB_PCOR                               GPIO_PCOR_REG(PTB_BASE_PTR)
#define GPIOB_PTOR                               GPIO_PTOR_REG(PTB_BASE_PTR)
#define GPIOB_PDIR                               GPIO_PDIR_REG(PTB_BASE_PTR)
#define GPIOB_PDDR                               GPIO_PDDR_REG(PTB_BASE_PTR)
/* PTC */
#define GPIOC_PDOR                               GPIO_PDOR_REG(PTC_BASE_PTR)
#define GPIOC_PSOR                               GPIO_PSOR_REG(PTC_BASE_PTR)
#define GPIOC_PCOR                               GPIO_PCOR_REG(PTC_BASE_PTR)
#define GPIOC_PTOR                               GPIO_PTOR_REG(PTC_BASE_PTR)
#define GPIOC_PDIR                               GPIO_PDIR_REG(PTC_BASE_PTR)
#define GPIOC_PDDR                               GPIO_PDDR_REG(PTC_BASE_PTR)
/* PTD */
#define GPIOD_PDOR                               GPIO_PDOR_REG(PTD_BASE_PTR)
#define GPIOD_PSOR                               GPIO_PSOR_REG(PTD_BASE_PTR)
#define GPIOD_PCOR                               GPIO_PCOR_REG(PTD_BASE_PTR)
#define GPIOD_PTOR                               GPIO_PTOR_REG(PTD_BASE_PTR)
#define GPIOD_PDIR                               GPIO_PDIR_REG(PTD_BASE_PTR)
#define GPIOD_PDDR                               GPIO_PDDR_REG(PTD_BASE_PTR)
/* PTE */
#define GPIOE_PDOR                               GPIO_PDOR_REG(PTE_BASE_PTR)
#define GPIOE_PSOR                               GPIO_PSOR_REG(PTE_BASE_PTR)
#define GPIOE_PCOR                               GPIO_PCOR_REG(PTE_BASE_PTR)
#define GPIOE_PTOR                               GPIO_PTOR_REG(PTE_BASE_PTR)
#define GPIOE_PDIR                               GPIO_PDIR_REG(PTE_BASE_PTR)
#define GPIOE_PDDR                               GPIO_PDDR_REG(PTE_BASE_PTR)

/**
 * @}
 */ /* end of group GPIO_Register_Accessor_Macros */


/**
 * @}
 */ /* end of group GPIO_Peripheral */


/* ----------------------------------------------------------------------------
   -- I2C
   ---------------------------------------------------------------------------- */

/**
 * @addtogroup I2C_Peripheral I2C
 * @{
 */

/** I2C - Peripheral register structure */
typedef struct I2C_MemMap {
  uint8_t A1;                                      /**< I2C Address Register 1, offset: 0x0 */
  uint8_t F;                                       /**< I2C Frequency Divider register, offset: 0x1 */
  uint8_t C1;                                      /**< I2C Control Register 1, offset: 0x2 */
  uint8_t S;                                       /**< I2C Status register, offset: 0x3 */
  uint8_t D;                                       /**< I2C Data I/O register, offset: 0x4 */
  uint8_t C2;                                      /**< I2C Control Register 2, offset: 0x5 */
  uint8_t FLT;                                     /**< I2C Programmable Input Glitch Filter register, offset: 0x6 */
  uint8_t RA;                                      /**< I2C Range Address register, offset: 0x7 */
  uint8_t SMB;                                     /**< I2C SMBus Control and Status register, offset: 0x8 */
  uint8_t A2;                                      /**< I2C Address Register 2, offset: 0x9 */
  uint8_t SLTH;                                    /**< I2C SCL Low Timeout Register High, offset: 0xA */
  uint8_t SLTL;                                    /**< I2C SCL Low Timeout Register Low, offset: 0xB */
} volatile *I2C_MemMapPtr;

/* ----------------------------------------------------------------------------
   -- I2C - Register accessor macros
   ---------------------------------------------------------------------------- */

/**
 * @addtogroup I2C_Register_Accessor_Macros I2C - Register accessor macros
 * @{
 */


/* I2C - Register accessors */
#define I2C_A1_REG(base)                         ((base)->A1)
#define I2C_F_REG(base)                          ((base)->F)
#define I2C_C1_REG(base)                         ((base)->C1)
#define I2C_S_REG(base)                          ((base)->S)
#define I2C_D_REG(base)                          ((base)->D)
#define I2C_C2_REG(base)                         ((base)->C2)
#define I2C_FLT_REG(base)                        ((base)->FLT)
#define I2C_RA_REG(base)                         ((base)->RA)
#define I2C_SMB_REG(base)                        ((base)->SMB)
#define I2C_A2_REG(base)                         ((base)->A2)
#define I2C_SLTH_REG(base)                       ((base)->SLTH)
#define I2C_SLTL_REG(base)                       ((base)->SLTL)

/**
 * @}
 */ /* end of group I2C_Register_Accessor_Macros */


/* ----------------------------------------------------------------------------
   -- I2C Register Masks
   ---------------------------------------------------------------------------- */

/**
 * @addtogroup I2C_Register_Masks I2C Register Masks
 * @{
 */

/* A1 Bit Fields */
#define I2C_A1_AD_MASK                           0xFEu
#define I2C_A1_AD_SHIFT                          1
#define I2C_A1_AD(x)                             (((uint8_t)(((uint8_t)(x))<<I2C_A1_AD_SHIFT))&I2C_A1_AD_MASK)
/* F Bit Fields */
#define I2C_F_ICR_MASK                           0x3Fu
#define I2C_F_ICR_SHIFT                          0
#define I2C_F_ICR(x)                             (((uint8_t)(((uint8_t)(x))<<I2C_F_ICR_SHIFT))&I2C_F_ICR_MASK)
#define I2C_F_MULT_MASK                          0xC0u
#define I2C_F_MULT_SHIFT                         6
#define I2C_F_MULT(x)                            (((uint8_t)(((uint8_t)(x))<<I2C_F_MULT_SHIFT))&I2C_F_MULT_MASK)
/* C1 Bit Fields */
#define I2C_C1_DMAEN_MASK                        0x1u
#define I2C_C1_DMAEN_SHIFT                       0
#define I2C_C1_WUEN_MASK                         0x2u
#define I2C_C1_WUEN_SHIFT                        1
#define I2C_C1_RSTA_MASK                         0x4u
#define I2C_C1_RSTA_SHIFT                        2
#define I2C_C1_TXAK_MASK                         0x8u
#define I2C_C1_TXAK_SHIFT                        3
#define I2C_C1_TX_MASK                           0x10u
#define I2C_C1_TX_SHIFT                          4
#define I2C_C1_MST_MASK                          0x20u
#define I2C_C1_MST_SHIFT                         5
#define I2C_C1_IICIE_MASK                        0x40u
#define I2C_C1_IICIE_SHIFT                       6
#define I2C_C1_IICEN_MASK                        0x80u
#define I2C_C1_IICEN_SHIFT                       7
/* S Bit Fields */
#define I2C_S_RXAK_MASK                          0x1u
#define I2C_S_RXAK_SHIFT                         0
#define I2C_S_IICIF_MASK                         0x2u
#define I2C_S_IICIF_SHIFT                        1
#define I2C_S_SRW_MASK                           0x4u
#define I2C_S_SRW_SHIFT                          2
#define I2C_S_RAM_MASK                           0x8u
#define I2C_S_RAM_SHIFT                          3
#define I2C_S_ARBL_MASK                          0x10u
#define I2C_S_ARBL_SHIFT                         4
#define I2C_S_BUSY_MASK                          0x20u
#define I2C_S_BUSY_SHIFT                         5
#define I2C_S_IAAS_MASK                          0x40u
#define I2C_S_IAAS_SHIFT                         6
#define I2C_S_TCF_MASK                           0x80u
#define I2C_S_TCF_SHIFT                          7
/* D Bit Fields */
#define I2C_D_DATA_MASK                          0xFFu
#define I2C_D_DATA_SHIFT                         0
#define I2C_D_DATA(x)                            (((uint8_t)(((uint8_t)(x))<<I2C_D_DATA_SHIFT))&I2C_D_DATA_MASK)
/* C2 Bit Fields */
#define I2C_C2_AD_MASK                           0x7u
#define I2C_C2_AD_SHIFT                          0
#define I2C_C2_AD(x)                             (((uint8_t)(((uint8_t)(x))<<I2C_C2_AD_SHIFT))&I2C_C2_AD_MASK)
#define I2C_C2_RMEN_MASK                         0x8u
#define I2C_C2_RMEN_SHIFT                        3
#define I2C_C2_SBRC_MASK                         0x10u
#define I2C_C2_SBRC_SHIFT                        4
#define I2C_C2_HDRS_MASK                         0x20u
#define I2C_C2_HDRS_SHIFT                        5
#define I2C_C2_ADEXT_MASK                        0x40u
#define I2C_C2_ADEXT_SHIFT                       6
#define I2C_C2_GCAEN_MASK                        0x80u
#define I2C_C2_GCAEN_SHIFT                       7
/* FLT Bit Fields */
#define I2C_FLT_FLT_MASK                         0x1Fu
#define I2C_FLT_FLT_SHIFT                        0
#define I2C_FLT_FLT(x)                           (((uint8_t)(((uint8_t)(x))<<I2C_FLT_FLT_SHIFT))&I2C_FLT_FLT_MASK)
#define I2C_FLT_STOPIE_MASK                      0x20u
#define I2C_FLT_STOPIE_SHIFT                     5
#define I2C_FLT_STOPF_MASK                       0x40u
#define I2C_FLT_STOPF_SHIFT                      6
#define I2C_FLT_SHEN_MASK                        0x80u
#define I2C_FLT_SHEN_SHIFT                       7
/* RA Bit Fields */
#define I2C_RA_RAD_MASK                          0xFEu
#define I2C_RA_RAD_SHIFT                         1
#define I2C_RA_RAD(x)                            (((uint8_t)(((uint8_t)(x))<<I2C_RA_RAD_SHIFT))&I2C_RA_RAD_MASK)
/* SMB Bit Fields */
#define I2C_SMB_SHTF2IE_MASK                     0x1u
#define I2C_SMB_SHTF2IE_SHIFT                    0
#define I2C_SMB_SHTF2_MASK                       0x2u
#define I2C_SMB_SHTF2_SHIFT                      1
#define I2C_SMB_SHTF1_MASK                       0x4u
#define I2C_SMB_SHTF1_SHIFT                      2
#define I2C_SMB_SLTF_MASK                        0x8u
#define I2C_SMB_SLTF_SHIFT                       3
#define I2C_SMB_TCKSEL_MASK                      0x10u
#define I2C_SMB_TCKSEL_SHIFT                     4
#define I2C_SMB_SIICAEN_MASK                     0x20u
#define I2C_SMB_SIICAEN_SHIFT                    5
#define I2C_SMB_ALERTEN_MASK                     0x40u
#define I2C_SMB_ALERTEN_SHIFT                    6
#define I2C_SMB_FACK_MASK                        0x80u
#define I2C_SMB_FACK_SHIFT                       7
/* A2 Bit Fields */
#define I2C_A2_SAD_MASK                          0xFEu
#define I2C_A2_SAD_SHIFT                         1
#define I2C_A2_SAD(x)                            (((uint8_t)(((uint8_t)(x))<<I2C_A2_SAD_SHIFT))&I2C_A2_SAD_MASK)
/* SLTH Bit Fields */
#define I2C_SLTH_SSLT_MASK                       0xFFu
#define I2C_SLTH_SSLT_SHIFT                      0
#define I2C_SLTH_SSLT(x)                         (((uint8_t)(((uint8_t)(x))<<I2C_SLTH_SSLT_SHIFT))&I2C_SLTH_SSLT_MASK)
/* SLTL Bit Fields */
#define I2C_SLTL_SSLT_MASK                       0xFFu
#define I2C_SLTL_SSLT_SHIFT                      0
#define I2C_SLTL_SSLT(x)                         (((uint8_t)(((uint8_t)(x))<<I2C_SLTL_SSLT_SHIFT))&I2C_SLTL_SSLT_MASK)

/**
 * @}
 */ /* end of group I2C_Register_Masks */


/* I2C - Peripheral instance base addresses */
/** Peripheral I2C0 base pointer */
#define I2C0_BASE_PTR                            ((I2C_MemMapPtr)0x40066000u)
/** Peripheral I2C1 base pointer */
#define I2C1_BASE_PTR                            ((I2C_MemMapPtr)0x40067000u)
/** Array initializer of I2C peripheral base pointers */
#define I2C_BASE_PTRS                            { I2C0_BASE_PTR, I2C1_BASE_PTR }

/* ----------------------------------------------------------------------------
   -- I2C - Register accessor macros
   ---------------------------------------------------------------------------- */

/**
 * @addtogroup I2C_Register_Accessor_Macros I2C - Register accessor macros
 * @{
 */


/* I2C - Register instance definitions */
/* I2C0 */
#define I2C0_A1                                  I2C_A1_REG(I2C0_BASE_PTR)
#define I2C0_F                                   I2C_F_REG(I2C0_BASE_PTR)
#define I2C0_C1                                  I2C_C1_REG(I2C0_BASE_PTR)
#define I2C0_S                                   I2C_S_REG(I2C0_BASE_PTR)
#define I2C0_D                                   I2C_D_REG(I2C0_BASE_PTR)
#define I2C0_C2                                  I2C_C2_REG(I2C0_BASE_PTR)
#define I2C0_FLT                                 I2C_FLT_REG(I2C0_BASE_PTR)
#define I2C0_RA                                  I2C_RA_REG(I2C0_BASE_PTR)
#define I2C0_SMB                                 I2C_SMB_REG(I2C0_BASE_PTR)
#define I2C0_A2                                  I2C_A2_REG(I2C0_BASE_PTR)
#define I2C0_SLTH                                I2C_SLTH_REG(I2C0_BASE_PTR)
#define I2C0_SLTL                                I2C_SLTL_REG(I2C0_BASE_PTR)
/* I2C1 */
#define I2C1_A1                                  I2C_A1_REG(I2C1_BASE_PTR)
#define I2C1_F                                   I2C_F_REG(I2C1_BASE_PTR)
#define I2C1_C1                                  I2C_C1_REG(I2C1_BASE_PTR)
#define I2C1_S                                   I2C_S_REG(I2C1_BASE_PTR)
#define I2C1_D                                   I2C_D_REG(I2C1_BASE_PTR)
#define I2C1_C2                                  I2C_C2_REG(I2C1_BASE_PTR)
#define I2C1_FLT                                 I2C_FLT_REG(I2C1_BASE_PTR)
#define I2C1_RA                                  I2C_RA_REG(I2C1_BASE_PTR)
#define I2C1_SMB                                 I2C_SMB_REG(I2C1_BASE_PTR)
#define I2C1_A2                                  I2C_A2_REG(I2C1_BASE_PTR)
#define I2C1_SLTH                                I2C_SLTH_REG(I2C1_BASE_PTR)
#define I2C1_SLTL                                I2C_SLTL_REG(I2C1_BASE_PTR)

/**
 * @}
 */ /* end of group I2C_Register_Accessor_Macros */


/**
 * @}
 */ /* end of group I2C_Peripheral */


/* ----------------------------------------------------------------------------
   -- I2S
   ---------------------------------------------------------------------------- */

/**
 * @addtogroup I2S_Peripheral I2S
 * @{
 */

/** I2S - Peripheral register structure */
typedef struct I2S_MemMap {
  uint32_t TCSR;                                   /**< SAI Transmit Control Register, offset: 0x0 */
  uint8_t RESERVED_0[4];
  uint32_t TCR2;                                   /**< SAI Transmit Configuration 2 Register, offset: 0x8 */
  uint32_t TCR3;                                   /**< SAI Transmit Configuration 3 Register, offset: 0xC */
  uint32_t TCR4;                                   /**< SAI Transmit Configuration 4 Register, offset: 0x10 */
  uint32_t TCR5;                                   /**< SAI Transmit Configuration 5 Register, offset: 0x14 */
  uint8_t RESERVED_1[8];
  uint32_t TDR[1];                                 /**< SAI Transmit Data Register, array offset: 0x20, array step: 0x4 */
  uint8_t RESERVED_2[60];
  uint32_t TMR;                                    /**< SAI Transmit Mask Register, offset: 0x60 */
  uint8_t RESERVED_3[28];
  uint32_t RCSR;                                   /**< SAI Receive Control Register, offset: 0x80 */
  uint8_t RESERVED_4[4];
  uint32_t RCR2;                                   /**< SAI Receive Configuration 2 Register, offset: 0x88 */
  uint32_t RCR3;                                   /**< SAI Receive Configuration 3 Register, offset: 0x8C */
  uint32_t RCR4;                                   /**< SAI Receive Configuration 4 Register, offset: 0x90 */
  uint32_t RCR5;                                   /**< SAI Receive Configuration 5 Register, offset: 0x94 */
  uint8_t RESERVED_5[8];
  uint32_t RDR[1];                                 /**< SAI Receive Data Register, array offset: 0xA0, array step: 0x4 */
  uint8_t RESERVED_6[60];
  uint32_t RMR;                                    /**< SAI Receive Mask Register, offset: 0xE0 */
  uint8_t RESERVED_7[28];
  uint32_t MCR;                                    /**< SAI MCLK Control Register, offset: 0x100 */
  uint32_t MDR;                                    /**< SAI MCLK Divide Register, offset: 0x104 */
} volatile *I2S_MemMapPtr;

/* ----------------------------------------------------------------------------
   -- I2S - Register accessor macros
   ---------------------------------------------------------------------------- */

/**
 * @addtogroup I2S_Register_Accessor_Macros I2S - Register accessor macros
 * @{
 */


/* I2S - Register accessors */
#define I2S_TCSR_REG(base)                       ((base)->TCSR)
#define I2S_TCR2_REG(base)                       ((base)->TCR2)
#define I2S_TCR3_REG(base)                       ((base)->TCR3)
#define I2S_TCR4_REG(base)                       ((base)->TCR4)
#define I2S_TCR5_REG(base)                       ((base)->TCR5)
#define I2S_TDR_REG(base,index)                  ((base)->TDR[index])
#define I2S_TMR_REG(base)                        ((base)->TMR)
#define I2S_RCSR_REG(base)                       ((base)->RCSR)
#define I2S_RCR2_REG(base)                       ((base)->RCR2)
#define I2S_RCR3_REG(base)                       ((base)->RCR3)
#define I2S_RCR4_REG(base)                       ((base)->RCR4)
#define I2S_RCR5_REG(base)                       ((base)->RCR5)
#define I2S_RDR_REG(base,index)                  ((base)->RDR[index])
#define I2S_RMR_REG(base)                        ((base)->RMR)
#define I2S_MCR_REG(base)                        ((base)->MCR)
#define I2S_MDR_REG(base)                        ((base)->MDR)

/**
 * @}
 */ /* end of group I2S_Register_Accessor_Macros */


/* ----------------------------------------------------------------------------
   -- I2S Register Masks
   ---------------------------------------------------------------------------- */

/**
 * @addtogroup I2S_Register_Masks I2S Register Masks
 * @{
 */

/* TCSR Bit Fields */
#define I2S_TCSR_FWDE_MASK                       0x2u
#define I2S_TCSR_FWDE_SHIFT                      1
#define I2S_TCSR_FWIE_MASK                       0x200u
#define I2S_TCSR_FWIE_SHIFT                      9
#define I2S_TCSR_FEIE_MASK                       0x400u
#define I2S_TCSR_FEIE_SHIFT                      10
#define I2S_TCSR_SEIE_MASK                       0x800u
#define I2S_TCSR_SEIE_SHIFT                      11
#define I2S_TCSR_WSIE_MASK                       0x1000u
#define I2S_TCSR_WSIE_SHIFT                      12
#define I2S_TCSR_FWF_MASK                        0x20000u
#define I2S_TCSR_FWF_SHIFT                       17
#define I2S_TCSR_FEF_MASK                        0x40000u
#define I2S_TCSR_FEF_SHIFT                       18
#define I2S_TCSR_SEF_MASK                        0x80000u
#define I2S_TCSR_SEF_SHIFT                       19
#define I2S_TCSR_WSF_MASK                        0x100000u
#define I2S_TCSR_WSF_SHIFT                       20
#define I2S_TCSR_SR_MASK                         0x1000000u
#define I2S_TCSR_SR_SHIFT                        24
#define I2S_TCSR_FR_MASK                         0x2000000u
#define I2S_TCSR_FR_SHIFT                        25
#define I2S_TCSR_BCE_MASK                        0x10000000u
#define I2S_TCSR_BCE_SHIFT                       28
#define I2S_TCSR_DBGE_MASK                       0x20000000u
#define I2S_TCSR_DBGE_SHIFT                      29
#define I2S_TCSR_STOPE_MASK                      0x40000000u
#define I2S_TCSR_STOPE_SHIFT                     30
#define I2S_TCSR_TE_MASK                         0x80000000u
#define I2S_TCSR_TE_SHIFT                        31
/* TCR2 Bit Fields */
#define I2S_TCR2_DIV_MASK                        0xFFu
#define I2S_TCR2_DIV_SHIFT                       0
#define I2S_TCR2_DIV(x)                          (((uint32_t)(((uint32_t)(x))<<I2S_TCR2_DIV_SHIFT))&I2S_TCR2_DIV_MASK)
#define I2S_TCR2_BCD_MASK                        0x1000000u
#define I2S_TCR2_BCD_SHIFT                       24
#define I2S_TCR2_BCP_MASK                        0x2000000u
#define I2S_TCR2_BCP_SHIFT                       25
#define I2S_TCR2_CLKMODE_MASK                    0xC000000u
#define I2S_TCR2_CLKMODE_SHIFT                   26
#define I2S_TCR2_CLKMODE(x)                      (((uint32_t)(((uint32_t)(x))<<I2S_TCR2_CLKMODE_SHIFT))&I2S_TCR2_CLKMODE_MASK)
/* TCR3 Bit Fields */
#define I2S_TCR3_WDFL_MASK                       0x1u
#define I2S_TCR3_WDFL_SHIFT                      0
#define I2S_TCR3_TCE_MASK                        0x10000u
#define I2S_TCR3_TCE_SHIFT                       16
/* TCR4 Bit Fields */
#define I2S_TCR4_FSD_MASK                        0x1u
#define I2S_TCR4_FSD_SHIFT                       0
#define I2S_TCR4_FSP_MASK                        0x2u
#define I2S_TCR4_FSP_SHIFT                       1
#define I2S_TCR4_FSE_MASK                        0x8u
#define I2S_TCR4_FSE_SHIFT                       3
#define I2S_TCR4_MF_MASK                         0x10u
#define I2S_TCR4_MF_SHIFT                        4
#define I2S_TCR4_SYWD_MASK                       0x1F00u
#define I2S_TCR4_SYWD_SHIFT                      8
#define I2S_TCR4_SYWD(x)                         (((uint32_t)(((uint32_t)(x))<<I2S_TCR4_SYWD_SHIFT))&I2S_TCR4_SYWD_MASK)
#define I2S_TCR4_FRSZ_MASK                       0x10000u
#define I2S_TCR4_FRSZ_SHIFT                      16
/* TCR5 Bit Fields */
#define I2S_TCR5_FBT_MASK                        0x1F00u
#define I2S_TCR5_FBT_SHIFT                       8
#define I2S_TCR5_FBT(x)                          (((uint32_t)(((uint32_t)(x))<<I2S_TCR5_FBT_SHIFT))&I2S_TCR5_FBT_MASK)
#define I2S_TCR5_W0W_MASK                        0x1F0000u
#define I2S_TCR5_W0W_SHIFT                       16
#define I2S_TCR5_W0W(x)                          (((uint32_t)(((uint32_t)(x))<<I2S_TCR5_W0W_SHIFT))&I2S_TCR5_W0W_MASK)
#define I2S_TCR5_WNW_MASK                        0x1F000000u
#define I2S_TCR5_WNW_SHIFT                       24
#define I2S_TCR5_WNW(x)                          (((uint32_t)(((uint32_t)(x))<<I2S_TCR5_WNW_SHIFT))&I2S_TCR5_WNW_MASK)
/* TDR Bit Fields */
#define I2S_TDR_TDR_MASK                         0xFFFFFFFFu
#define I2S_TDR_TDR_SHIFT                        0
#define I2S_TDR_TDR(x)                           (((uint32_t)(((uint32_t)(x))<<I2S_TDR_TDR_SHIFT))&I2S_TDR_TDR_MASK)
/* TMR Bit Fields */
#define I2S_TMR_TWM_MASK                         0x3u
#define I2S_TMR_TWM_SHIFT                        0
#define I2S_TMR_TWM(x)                           (((uint32_t)(((uint32_t)(x))<<I2S_TMR_TWM_SHIFT))&I2S_TMR_TWM_MASK)
/* RCSR Bit Fields */
#define I2S_RCSR_FWDE_MASK                       0x2u
#define I2S_RCSR_FWDE_SHIFT                      1
#define I2S_RCSR_FWIE_MASK                       0x200u
#define I2S_RCSR_FWIE_SHIFT                      9
#define I2S_RCSR_FEIE_MASK                       0x400u
#define I2S_RCSR_FEIE_SHIFT                      10
#define I2S_RCSR_SEIE_MASK                       0x800u
#define I2S_RCSR_SEIE_SHIFT                      11
#define I2S_RCSR_WSIE_MASK                       0x1000u
#define I2S_RCSR_WSIE_SHIFT                      12
#define I2S_RCSR_FWF_MASK                        0x20000u
#define I2S_RCSR_FWF_SHIFT                       17
#define I2S_RCSR_FEF_MASK                        0x40000u
#define I2S_RCSR_FEF_SHIFT                       18
#define I2S_RCSR_SEF_MASK                        0x80000u
#define I2S_RCSR_SEF_SHIFT                       19
#define I2S_RCSR_WSF_MASK                        0x100000u
#define I2S_RCSR_WSF_SHIFT                       20
#define I2S_RCSR_SR_MASK                         0x1000000u
#define I2S_RCSR_SR_SHIFT                        24
#define I2S_RCSR_FR_MASK                         0x2000000u
#define I2S_RCSR_FR_SHIFT                        25
#define I2S_RCSR_BCE_MASK                        0x10000000u
#define I2S_RCSR_BCE_SHIFT                       28
#define I2S_RCSR_DBGE_MASK                       0x20000000u
#define I2S_RCSR_DBGE_SHIFT                      29
#define I2S_RCSR_STOPE_MASK                      0x40000000u
#define I2S_RCSR_STOPE_SHIFT                     30
#define I2S_RCSR_RE_MASK                         0x80000000u
#define I2S_RCSR_RE_SHIFT                        31
/* RCR2 Bit Fields */
#define I2S_RCR2_DIV_MASK                        0xFFu
#define I2S_RCR2_DIV_SHIFT                       0
#define I2S_RCR2_DIV(x)                          (((uint32_t)(((uint32_t)(x))<<I2S_RCR2_DIV_SHIFT))&I2S_RCR2_DIV_MASK)
#define I2S_RCR2_BCD_MASK                        0x1000000u
#define I2S_RCR2_BCD_SHIFT                       24
#define I2S_RCR2_BCP_MASK                        0x2000000u
#define I2S_RCR2_BCP_SHIFT                       25
#define I2S_RCR2_CLKMODE_MASK                    0xC000000u
#define I2S_RCR2_CLKMODE_SHIFT                   26
#define I2S_RCR2_CLKMODE(x)                      (((uint32_t)(((uint32_t)(x))<<I2S_RCR2_CLKMODE_SHIFT))&I2S_RCR2_CLKMODE_MASK)
/* RCR3 Bit Fields */
#define I2S_RCR3_WDFL_MASK                       0x1u
#define I2S_RCR3_WDFL_SHIFT                      0
#define I2S_RCR3_RCE_MASK                        0x10000u
#define I2S_RCR3_RCE_SHIFT                       16
/* RCR4 Bit Fields */
#define I2S_RCR4_FSD_MASK                        0x1u
#define I2S_RCR4_FSD_SHIFT                       0
#define I2S_RCR4_FSP_MASK                        0x2u
#define I2S_RCR4_FSP_SHIFT                       1
#define I2S_RCR4_FSE_MASK                        0x8u
#define I2S_RCR4_FSE_SHIFT                       3
#define I2S_RCR4_MF_MASK                         0x10u
#define I2S_RCR4_MF_SHIFT                        4
#define I2S_RCR4_SYWD_MASK                       0x1F00u
#define I2S_RCR4_SYWD_SHIFT                      8
#define I2S_RCR4_SYWD(x)                         (((uint32_t)(((uint32_t)(x))<<I2S_RCR4_SYWD_SHIFT))&I2S_RCR4_SYWD_MASK)
#define I2S_RCR4_FRSZ_MASK                       0x10000u
#define I2S_RCR4_FRSZ_SHIFT                      16
/* RCR5 Bit Fields */
#define I2S_RCR5_FBT_MASK                        0x1F00u
#define I2S_RCR5_FBT_SHIFT                       8
#define I2S_RCR5_FBT(x)                          (((uint32_t)(((uint32_t)(x))<<I2S_RCR5_FBT_SHIFT))&I2S_RCR5_FBT_MASK)
#define I2S_RCR5_W0W_MASK                        0x1F0000u
#define I2S_RCR5_W0W_SHIFT                       16
#define I2S_RCR5_W0W(x)                          (((uint32_t)(((uint32_t)(x))<<I2S_RCR5_W0W_SHIFT))&I2S_RCR5_W0W_MASK)
#define I2S_RCR5_WNW_MASK                        0x1F000000u
#define I2S_RCR5_WNW_SHIFT                       24
#define I2S_RCR5_WNW(x)                          (((uint32_t)(((uint32_t)(x))<<I2S_RCR5_WNW_SHIFT))&I2S_RCR5_WNW_MASK)
/* RDR Bit Fields */
#define I2S_RDR_RDR_MASK                         0xFFFFFFFFu
#define I2S_RDR_RDR_SHIFT                        0
#define I2S_RDR_RDR(x)                           (((uint32_t)(((uint32_t)(x))<<I2S_RDR_RDR_SHIFT))&I2S_RDR_RDR_MASK)
/* RMR Bit Fields */
#define I2S_RMR_RWM_MASK                         0x3u
#define I2S_RMR_RWM_SHIFT                        0
#define I2S_RMR_RWM(x)                           (((uint32_t)(((uint32_t)(x))<<I2S_RMR_RWM_SHIFT))&I2S_RMR_RWM_MASK)
/* MCR Bit Fields */
#define I2S_MCR_MICS_MASK                        0x3000000u
#define I2S_MCR_MICS_SHIFT                       24
#define I2S_MCR_MICS(x)                          (((uint32_t)(((uint32_t)(x))<<I2S_MCR_MICS_SHIFT))&I2S_MCR_MICS_MASK)
#define I2S_MCR_MOE_MASK                         0x40000000u
#define I2S_MCR_MOE_SHIFT                        30
#define I2S_MCR_DUF_MASK                         0x80000000u
#define I2S_MCR_DUF_SHIFT                        31
/* MDR Bit Fields */
#define I2S_MDR_DIVIDE_MASK                      0xFFFu
#define I2S_MDR_DIVIDE_SHIFT                     0
#define I2S_MDR_DIVIDE(x)                        (((uint32_t)(((uint32_t)(x))<<I2S_MDR_DIVIDE_SHIFT))&I2S_MDR_DIVIDE_MASK)
#define I2S_MDR_FRACT_MASK                       0xFF000u
#define I2S_MDR_FRACT_SHIFT                      12
#define I2S_MDR_FRACT(x)                         (((uint32_t)(((uint32_t)(x))<<I2S_MDR_FRACT_SHIFT))&I2S_MDR_FRACT_MASK)

/**
 * @}
 */ /* end of group I2S_Register_Masks */


/* I2S - Peripheral instance base addresses */
/** Peripheral I2S0 base pointer */
#define I2S0_BASE_PTR                            ((I2S_MemMapPtr)0x4002F000u)
/** Array initializer of I2S peripheral base pointers */
#define I2S_BASE_PTRS                            { I2S0_BASE_PTR }

/* ----------------------------------------------------------------------------
   -- I2S - Register accessor macros
   ---------------------------------------------------------------------------- */

/**
 * @addtogroup I2S_Register_Accessor_Macros I2S - Register accessor macros
 * @{
 */


/* I2S - Register instance definitions */
/* I2S0 */
#define I2S_TCSR                                 I2S_TCSR_REG(I2S0_BASE_PTR)
#define I2S_TCR2                                 I2S_TCR2_REG(I2S0_BASE_PTR)
#define I2S_TCR3                                 I2S_TCR3_REG(I2S0_BASE_PTR)
#define I2S_TCR4                                 I2S_TCR4_REG(I2S0_BASE_PTR)
#define I2S_TCR5                                 I2S_TCR5_REG(I2S0_BASE_PTR)
#define I2S_TDR0                                 I2S_TDR_REG(I2S0_BASE_PTR,0)
#define I2S_TMR                                  I2S_TMR_REG(I2S0_BASE_PTR)
#define I2S_RCSR                                 I2S_RCSR_REG(I2S0_BASE_PTR)
#define I2S_RCR2                                 I2S_RCR2_REG(I2S0_BASE_PTR)
#define I2S_RCR3                                 I2S_RCR3_REG(I2S0_BASE_PTR)
#define I2S_RCR4                                 I2S_RCR4_REG(I2S0_BASE_PTR)
#define I2S_RCR5                                 I2S_RCR5_REG(I2S0_BASE_PTR)
#define I2S_RDR0                                 I2S_RDR_REG(I2S0_BASE_PTR,0)
#define I2S_RMR                                  I2S_RMR_REG(I2S0_BASE_PTR)
#define I2S_MCR                                  I2S_MCR_REG(I2S0_BASE_PTR)
#define I2S_MDR                                  I2S_MDR_REG(I2S0_BASE_PTR)

/* I2S - Register array accessors */
#define I2S0_TDR(index)                          I2S_TDR_REG(I2S0_BASE_PTR,index)
#define I2S0_RDR(index)                          I2S_RDR_REG(I2S0_BASE_PTR,index)

/**
 * @}
 */ /* end of group I2S_Register_Accessor_Macros */


/**
 * @}
 */ /* end of group I2S_Peripheral */


/* ----------------------------------------------------------------------------
   -- LLWU
   ---------------------------------------------------------------------------- */

/**
 * @addtogroup LLWU_Peripheral LLWU
 * @{
 */

/** LLWU - Peripheral register structure */
typedef struct LLWU_MemMap {
  uint8_t PE1;                                     /**< LLWU Pin Enable 1 register, offset: 0x0 */
  uint8_t PE2;                                     /**< LLWU Pin Enable 2 register, offset: 0x1 */
  uint8_t PE3;                                     /**< LLWU Pin Enable 3 register, offset: 0x2 */
  uint8_t PE4;                                     /**< LLWU Pin Enable 4 register, offset: 0x3 */
  uint8_t ME;                                      /**< LLWU Module Enable register, offset: 0x4 */
  uint8_t F1;                                      /**< LLWU Flag 1 register, offset: 0x5 */
  uint8_t F2;                                      /**< LLWU Flag 2 register, offset: 0x6 */
  uint8_t F3;                                      /**< LLWU Flag 3 register, offset: 0x7 */
  uint8_t FILT1;                                   /**< LLWU Pin Filter 1 register, offset: 0x8 */
  uint8_t FILT2;                                   /**< LLWU Pin Filter 2 register, offset: 0x9 */
} volatile *LLWU_MemMapPtr;

/* ----------------------------------------------------------------------------
   -- LLWU - Register accessor macros
   ---------------------------------------------------------------------------- */

/**
 * @addtogroup LLWU_Register_Accessor_Macros LLWU - Register accessor macros
 * @{
 */


/* LLWU - Register accessors */
#define LLWU_PE1_REG(base)                       ((base)->PE1)
#define LLWU_PE2_REG(base)                       ((base)->PE2)
#define LLWU_PE3_REG(base)                       ((base)->PE3)
#define LLWU_PE4_REG(base)                       ((base)->PE4)
#define LLWU_ME_REG(base)                        ((base)->ME)
#define LLWU_F1_REG(base)                        ((base)->F1)
#define LLWU_F2_REG(base)                        ((base)->F2)
#define LLWU_F3_REG(base)                        ((base)->F3)
#define LLWU_FILT1_REG(base)                     ((base)->FILT1)
#define LLWU_FILT2_REG(base)                     ((base)->FILT2)

/**
 * @}
 */ /* end of group LLWU_Register_Accessor_Macros */


/* ----------------------------------------------------------------------------
   -- LLWU Register Masks
   ---------------------------------------------------------------------------- */

/**
 * @addtogroup LLWU_Register_Masks LLWU Register Masks
 * @{
 */
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
